cozdas/CozScan2020/Photos/20190418_014314.jpg

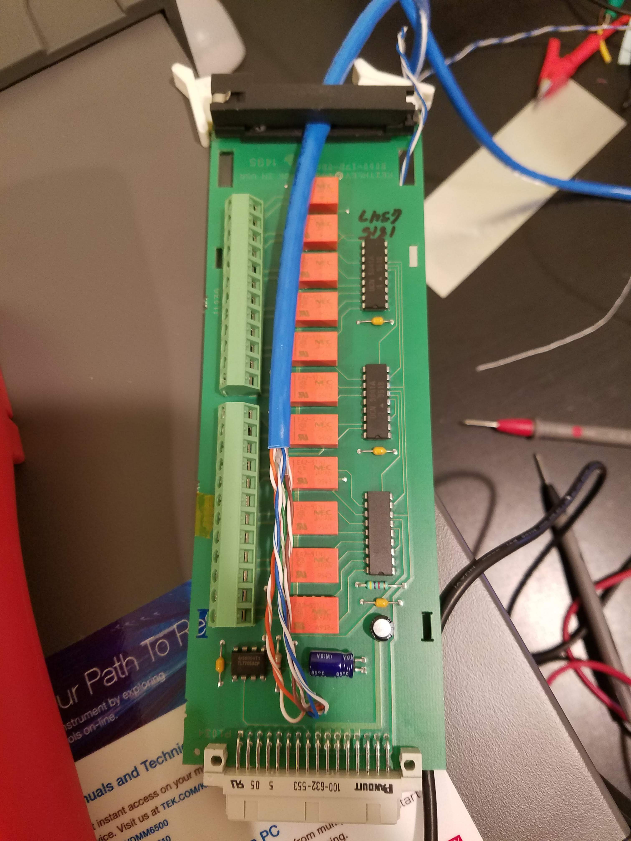
Photos/20190418_014314.jpg
