cozdas/CozScan2020/Photos/20190418_014336.jpg

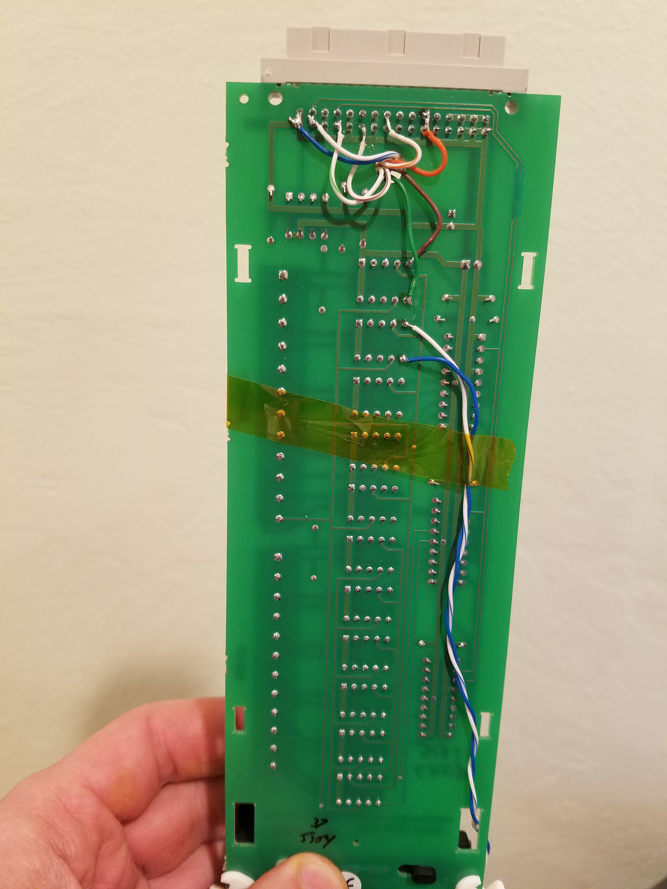
Photos/20190418_014336.jpg
