cozdas/CozScan2020/Photos/20190418_014348.jpg

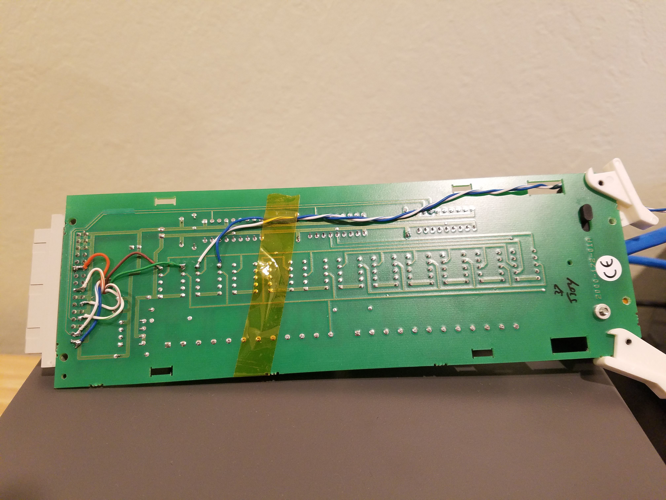
Photos/20190418_014348.jpg
