cozdas/CozScan2020/Photos/20190418_014632.jpg

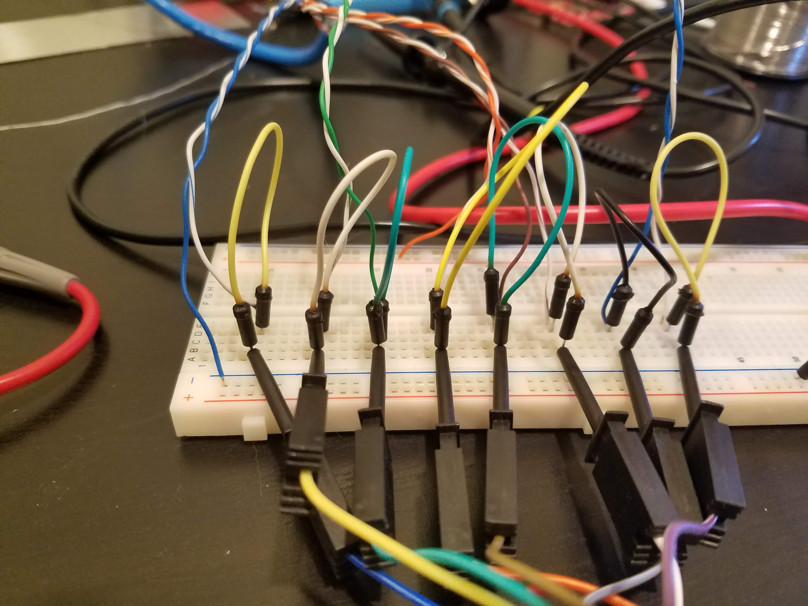
Photos/20190418_014632.jpg
