cozdas/CozScan2020/Photos/20190418_014634.jpg

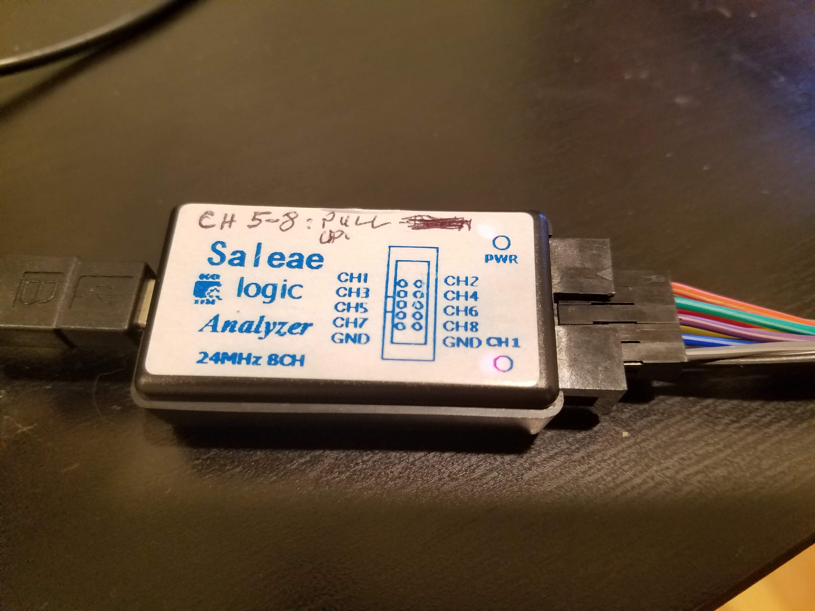
Photos/20190418_014634.jpg
