cozdas/CozScan2020/Photos/20190419_014511.jpg

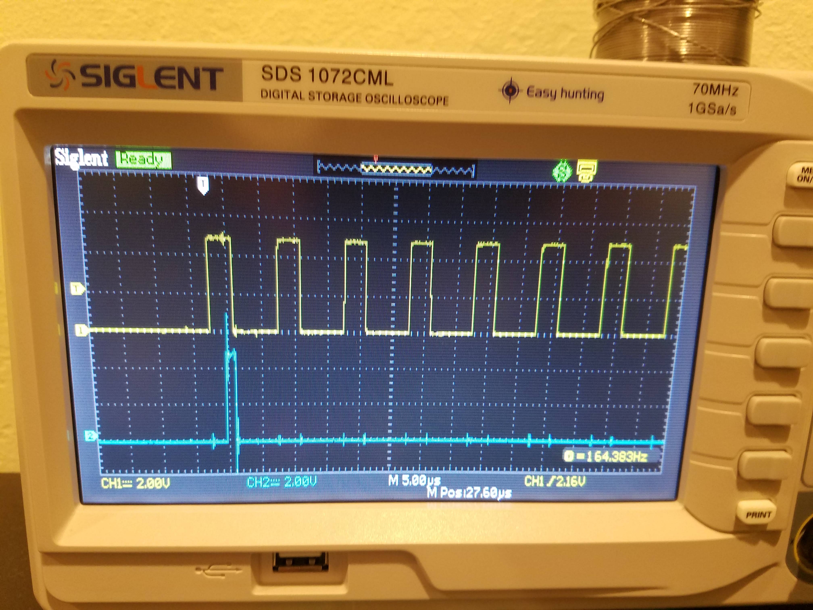
Photos/20190419_014511.jpg
