cozdas/CozScan2020/Photos/20190419_014527.jpg

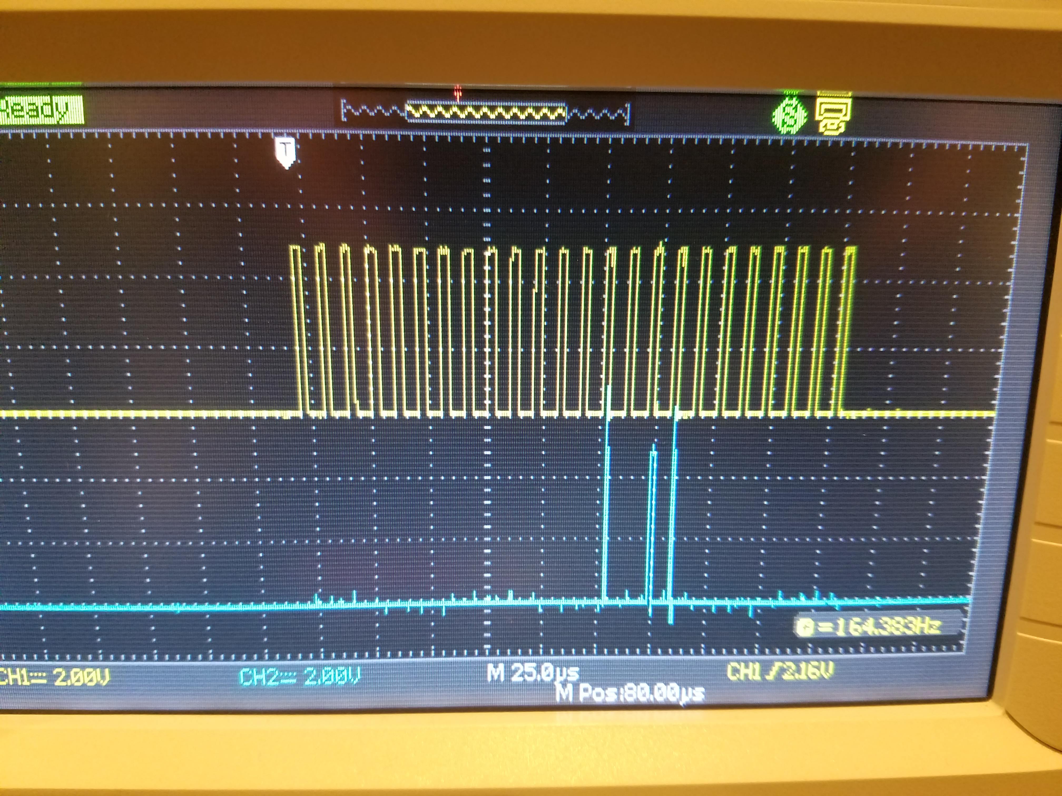
Photos/20190419_014527.jpg
