cozdas/CozScan2020/Photos/20190504_023727.jpg

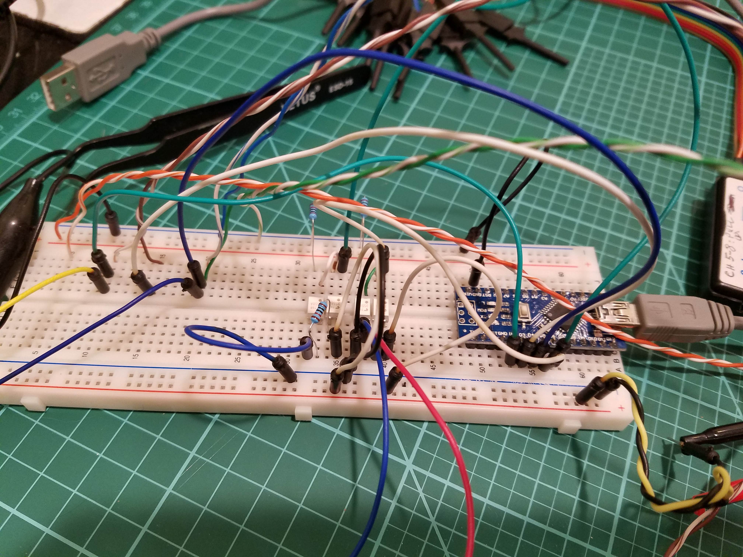
Photos/20190504_023727.jpg
