cozdas/CozScan2020/Photos/20190504_023732.jpg

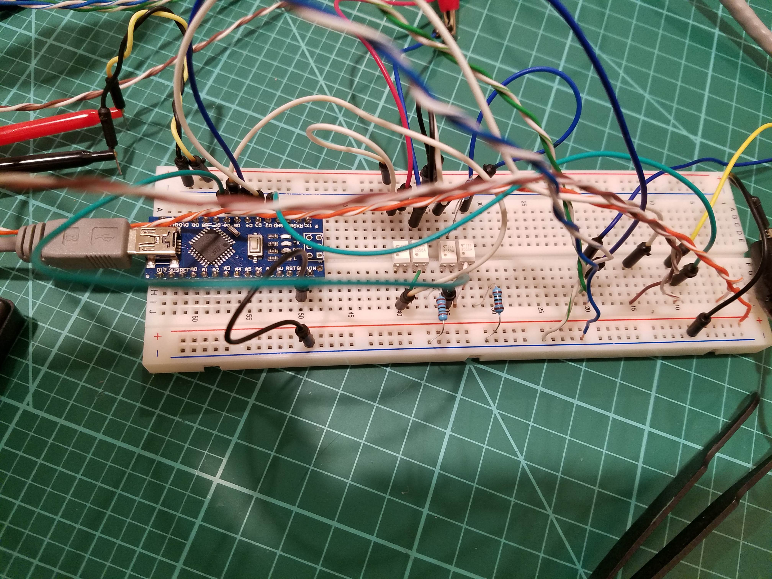
Photos/20190504_023732.jpg
