cozdas/CozScan2020/Photos/20190504_023738.jpg

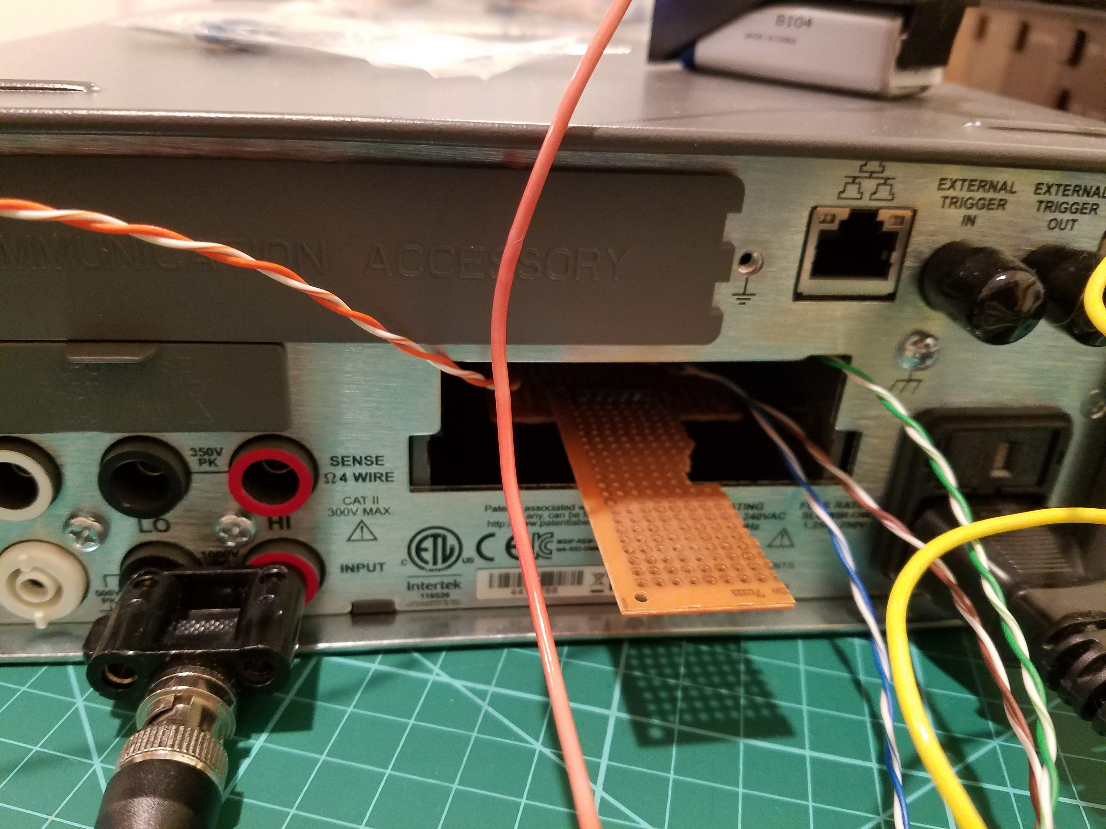
Photos/20190504_023738.jpg
