cozdas/CozScan2020/Photos/20190507_173310.jpg

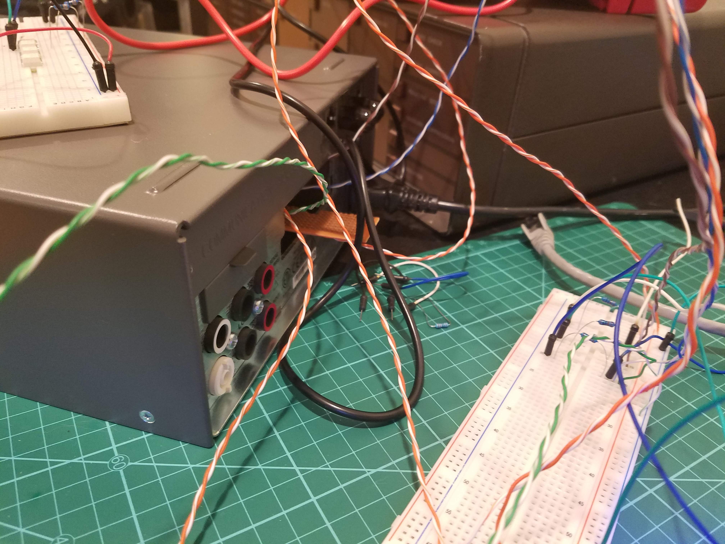
Photos/20190507_173310.jpg
