cozdas/CozScan2020/Photos/20190507_173314.jpg

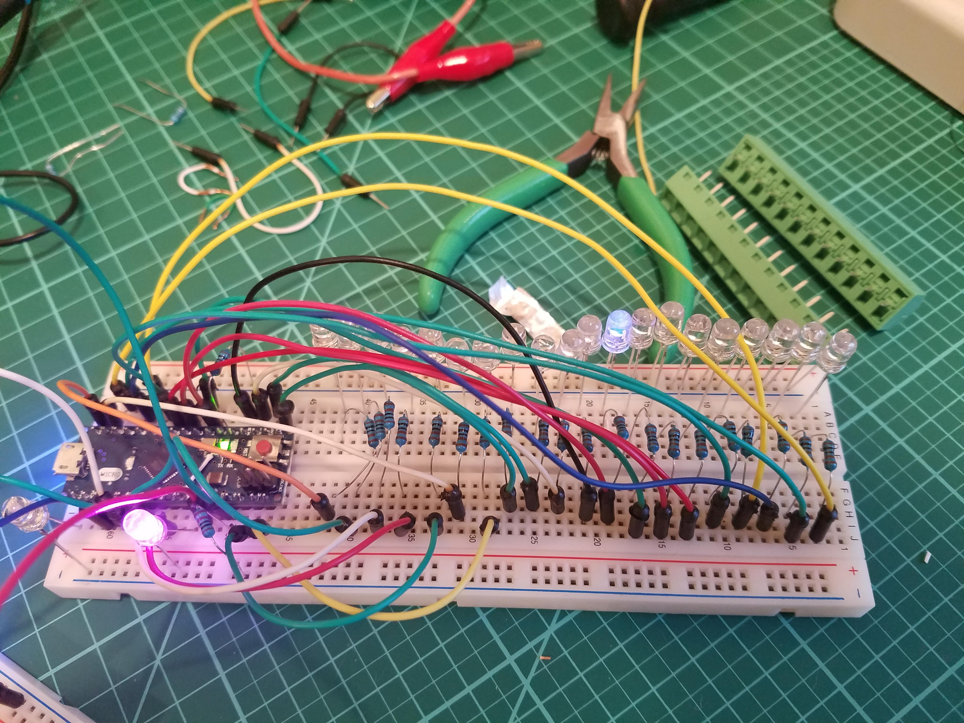
Photos/20190507_173314.jpg
