cozdas/CozScan2020/Photos/20190507_173317.jpg

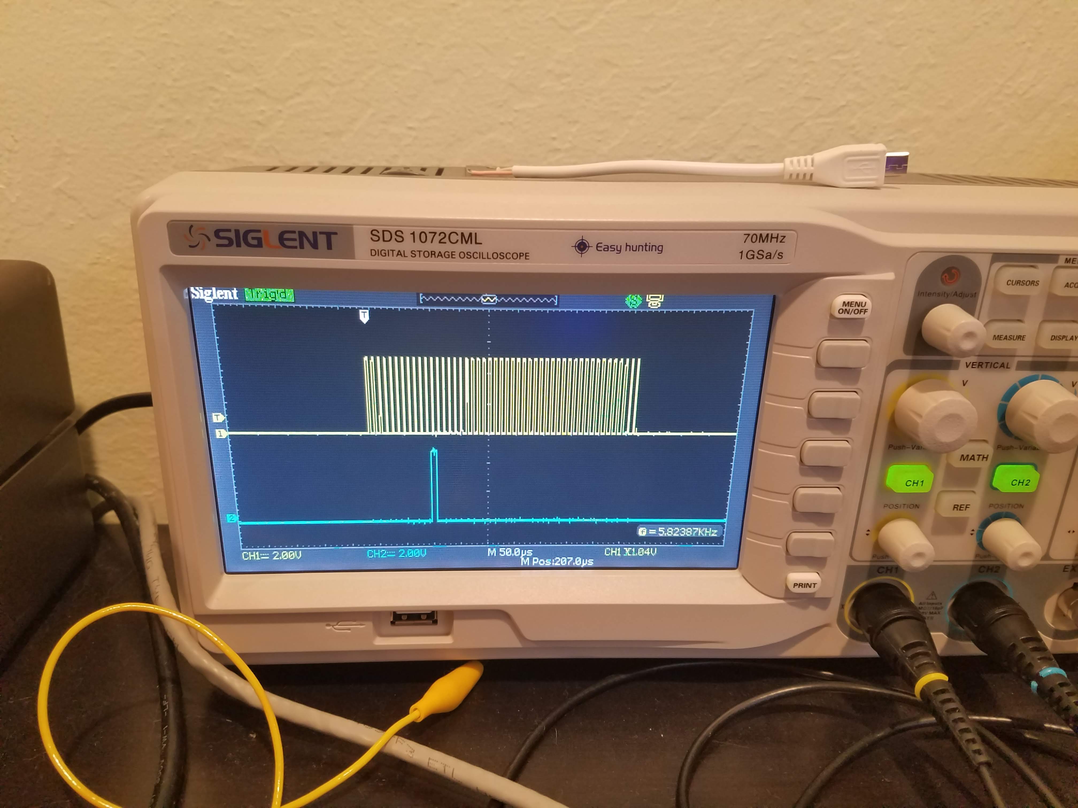
Photos/20190507_173317.jpg
