cozdas/CozScan2020/Photos/20190507_180959.jpg

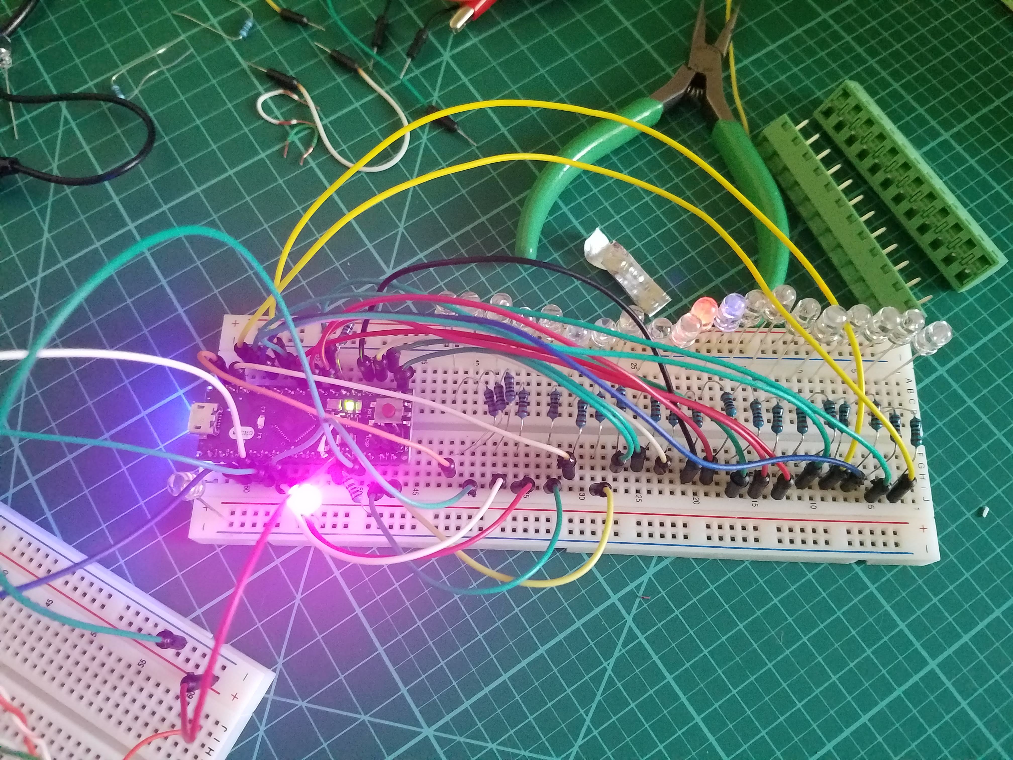
Photos/20190507_180959.jpg
