cozdas/CozScan2020/Photos/20190507_181006.jpg

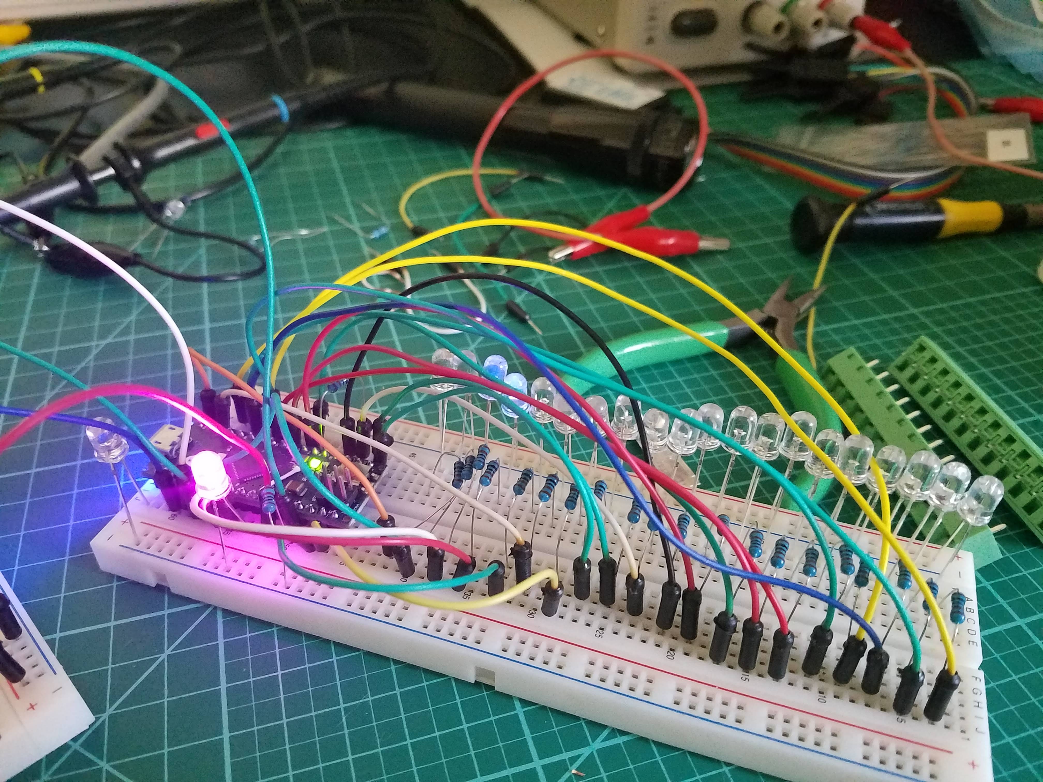
Photos/20190507_181006.jpg
