cozdas/CozScan2020/Photos/20190507_181008.jpg

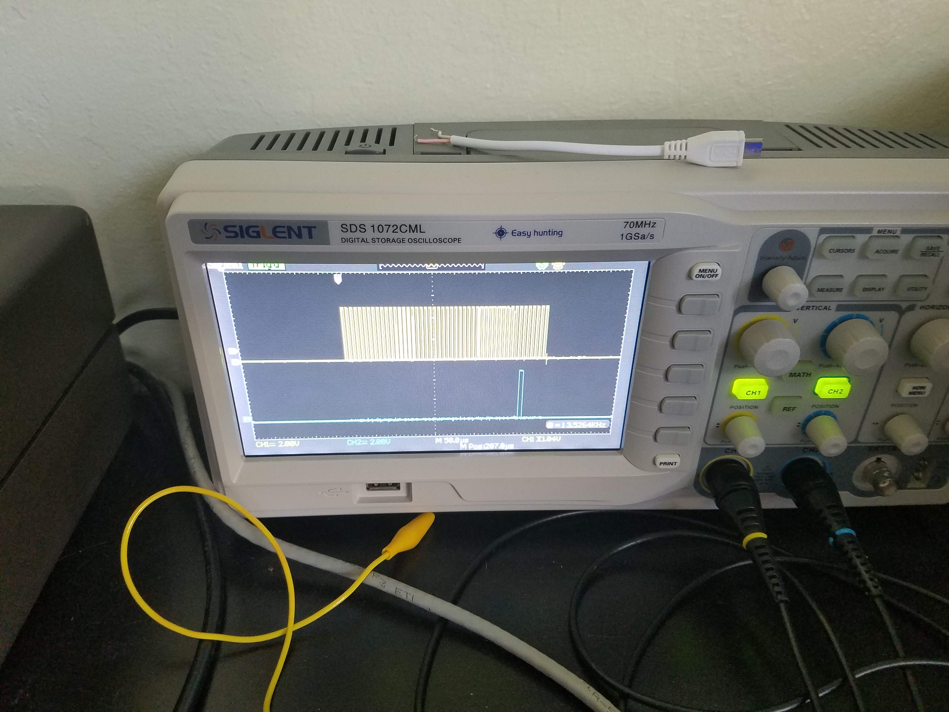
Photos/20190507_181008.jpg
