cozdas/CozScan2020/Photos/20190508_041642.jpg

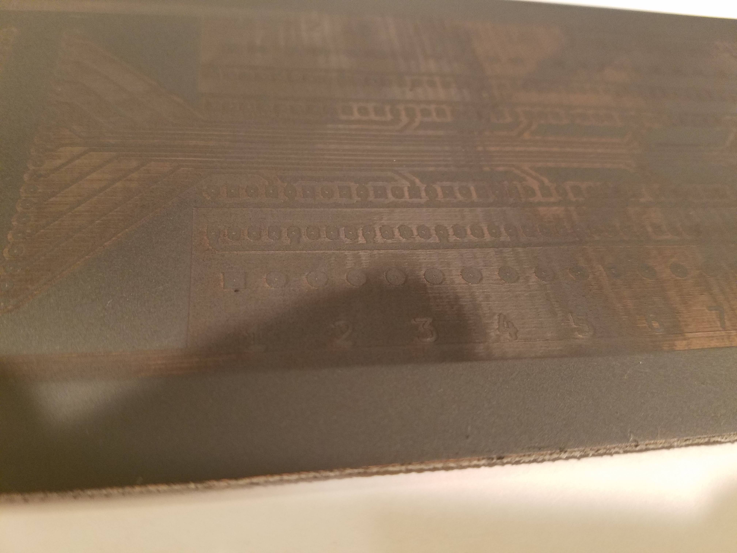
Photos/20190508_041642.jpg
