cozdas/CozScan2020/Photos/20190508_041654.jpg

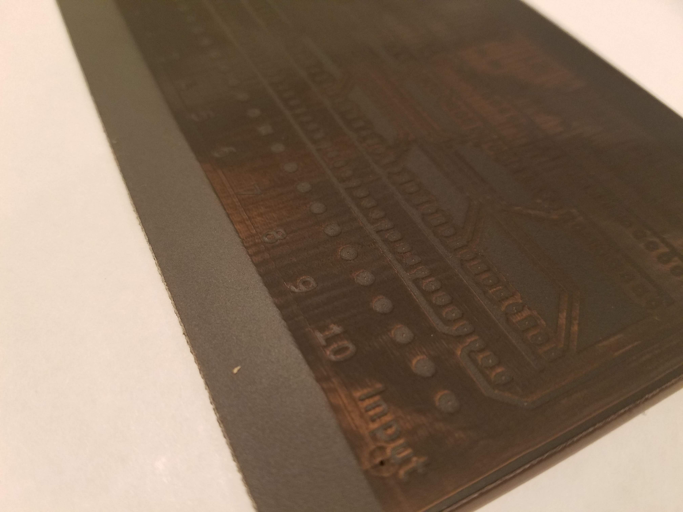
Photos/20190508_041654.jpg
