cozdas/CozScan2020/Photos/20190508_041701.jpg

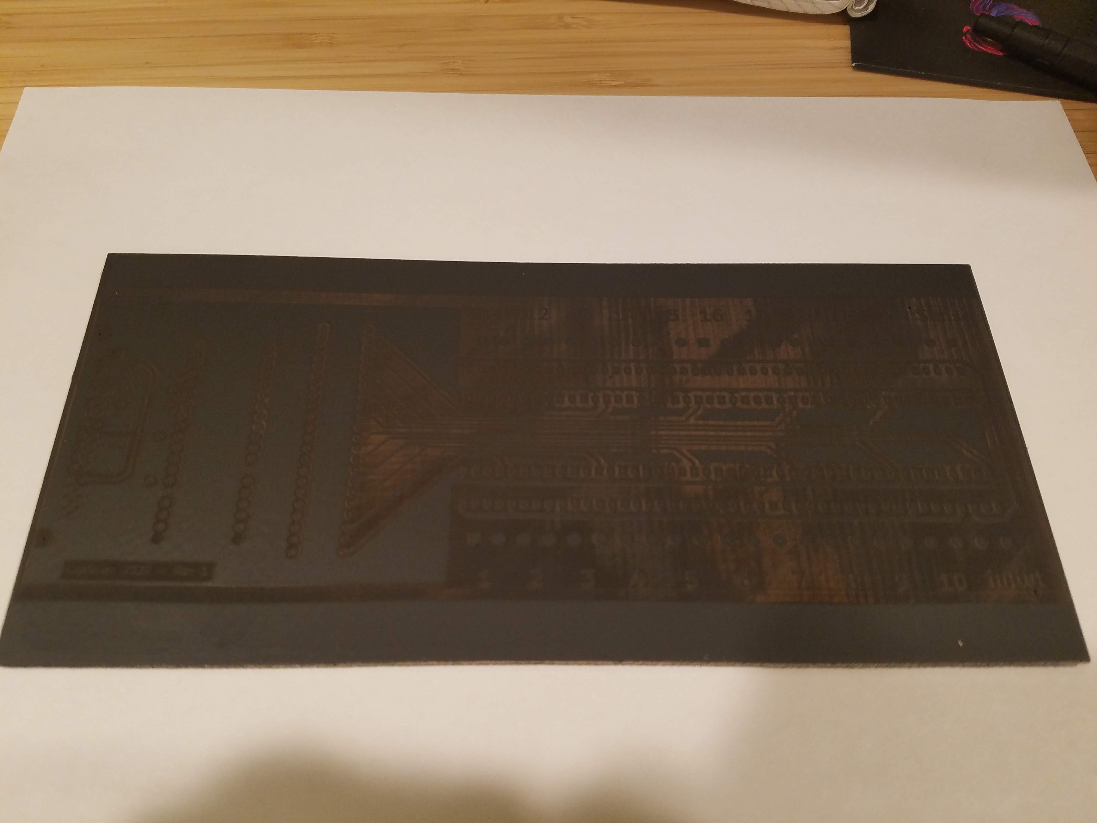
Photos/20190508_041701.jpg
