cozdas/CozScan2020/Photos/20190508_041709.jpg

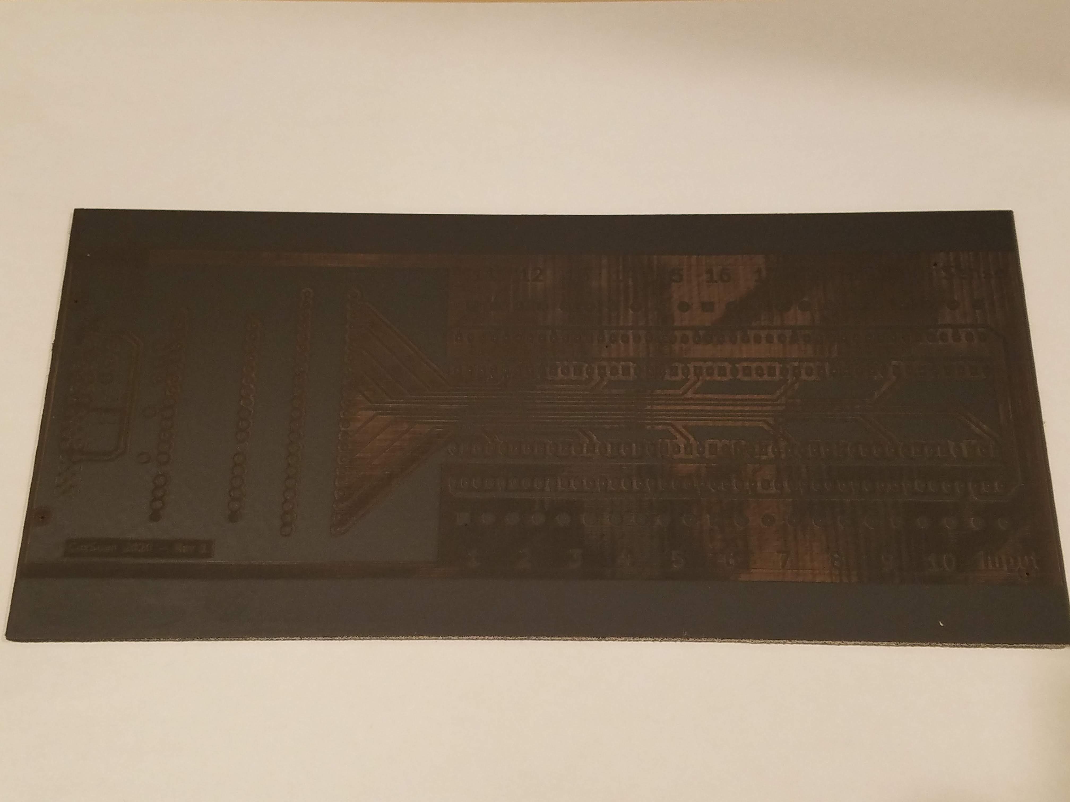
Photos/20190508_041709.jpg
