cozdas/CozScan2020/Photos/20190508_041718.jpg

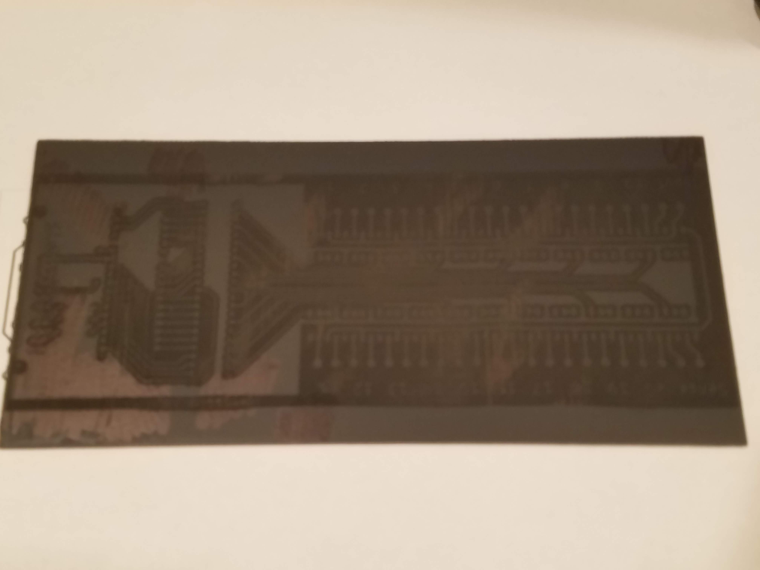
Photos/20190508_041718.jpg
