cozdas/CozScan2020/Photos/20190508_041728.jpg

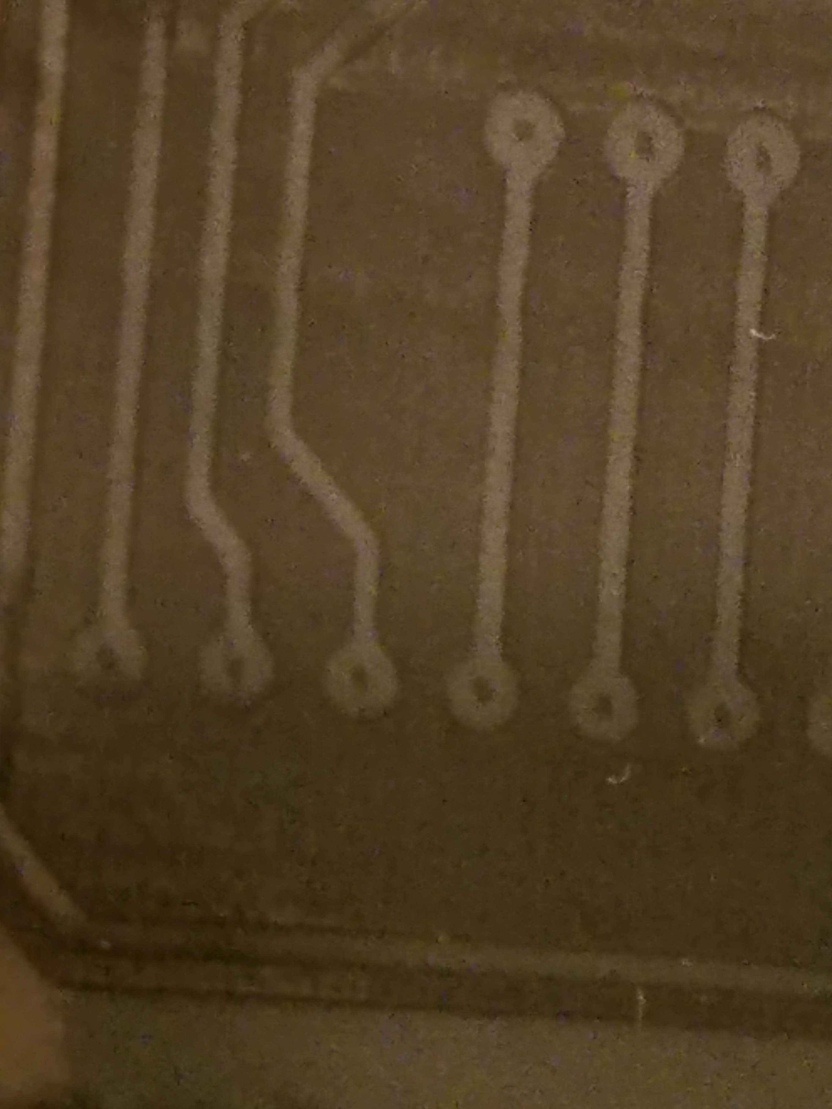
Photos/20190508_041728.jpg
