cozdas/CozScan2020/Photos/20190508_041800.jpg

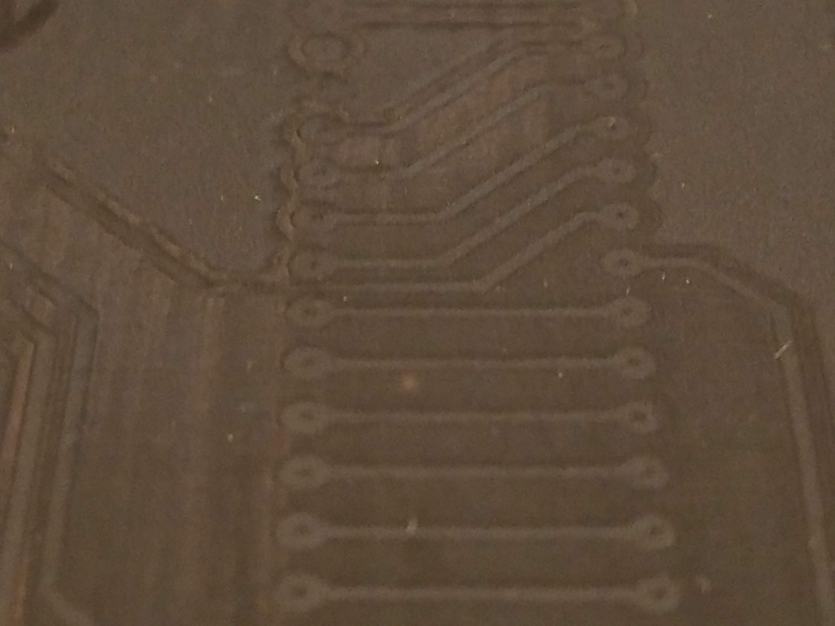
Photos/20190508_041800.jpg
