cozdas/CozScan2020/Photos/20190508_041806.jpg

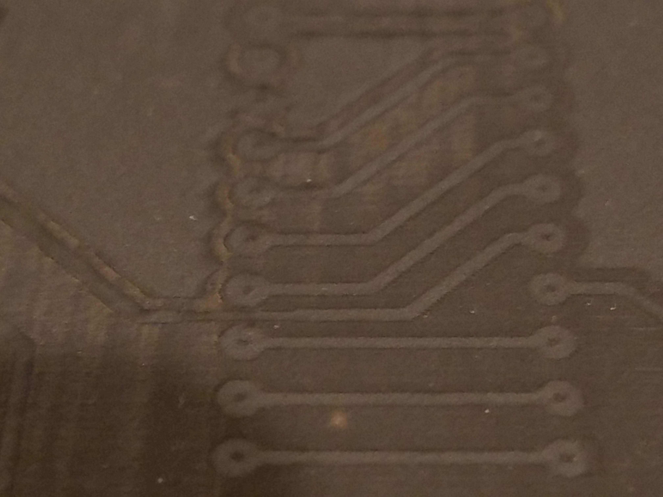
Photos/20190508_041806.jpg
