cozdas/CozScan2020/Photos/20190508_041815.jpg

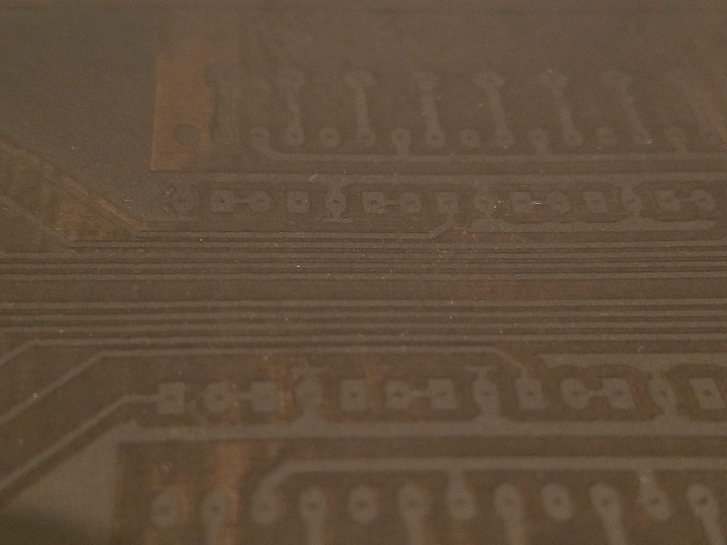
Photos/20190508_041815.jpg
