cozdas/CozScan2020/Photos/20190508_041832.jpg

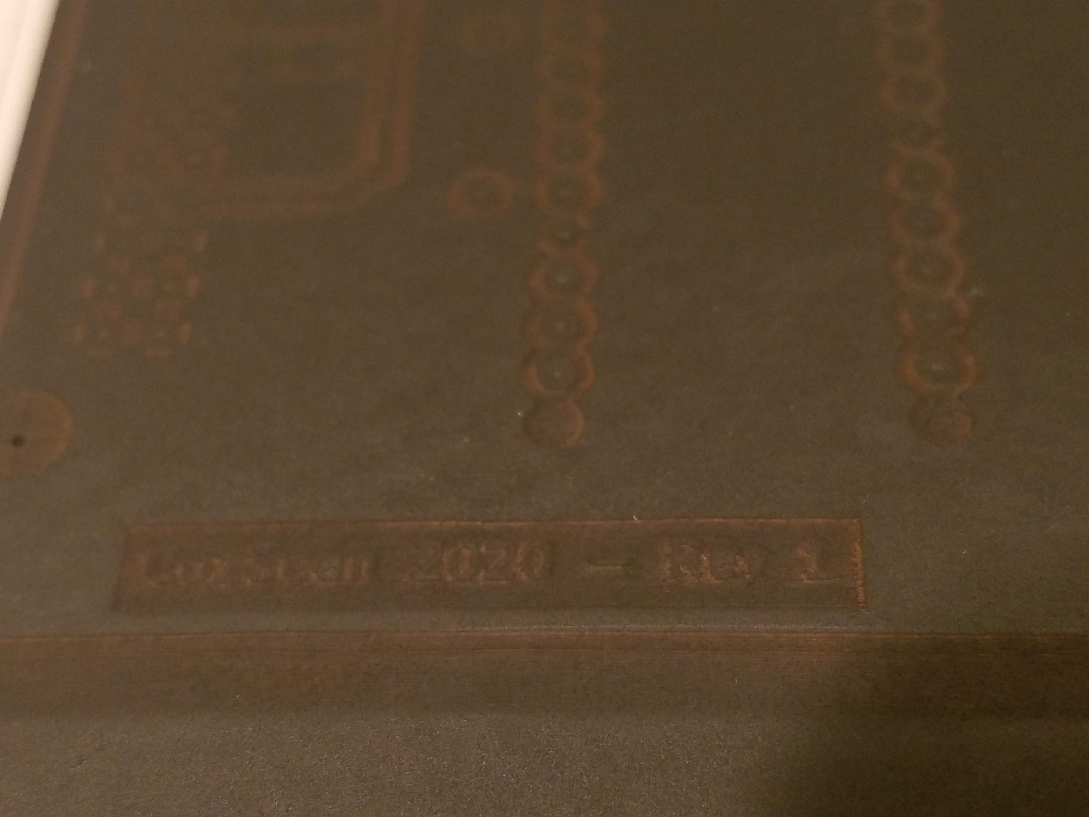
Photos/20190508_041832.jpg
