cozdas/CozScan2020/Photos/20190508_041854.jpg

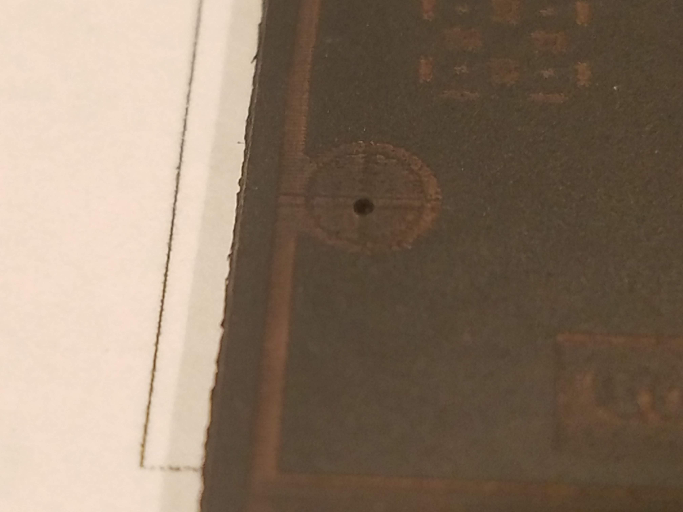
Photos/20190508_041854.jpg
