cozdas/CozScan2020/Photos/20190508_041901.jpg

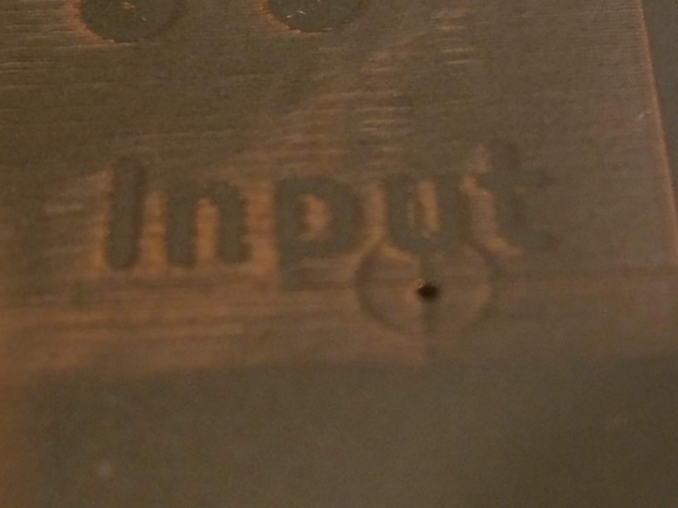
Photos/20190508_041901.jpg
