cozdas/CozScan2020/Photos/20190508_041907.jpg

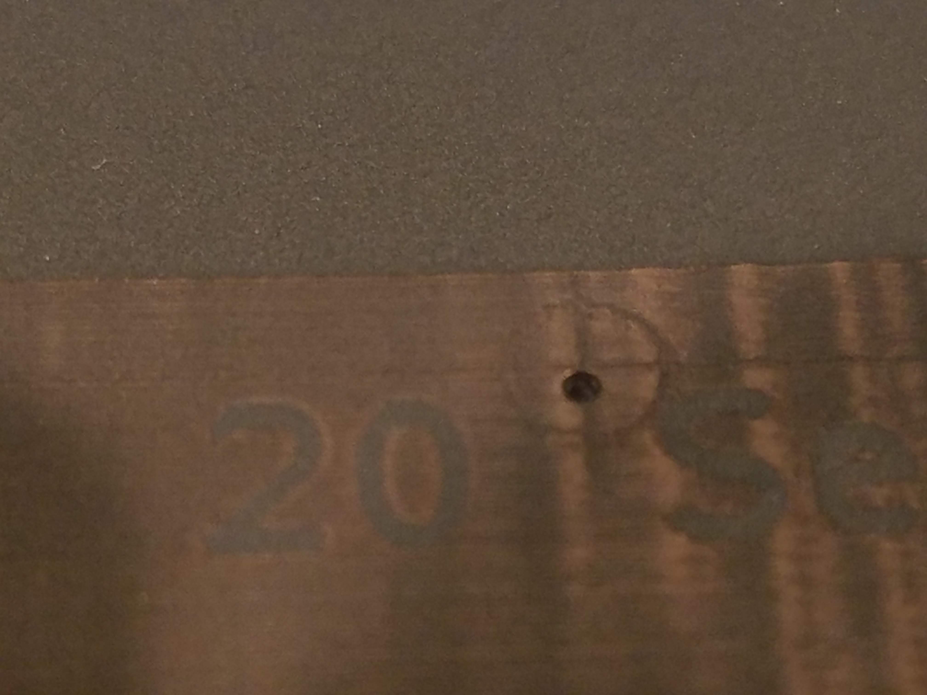
Photos/20190508_041907.jpg
