cozdas/CozScan2020/Photos/20190508_041913.jpg

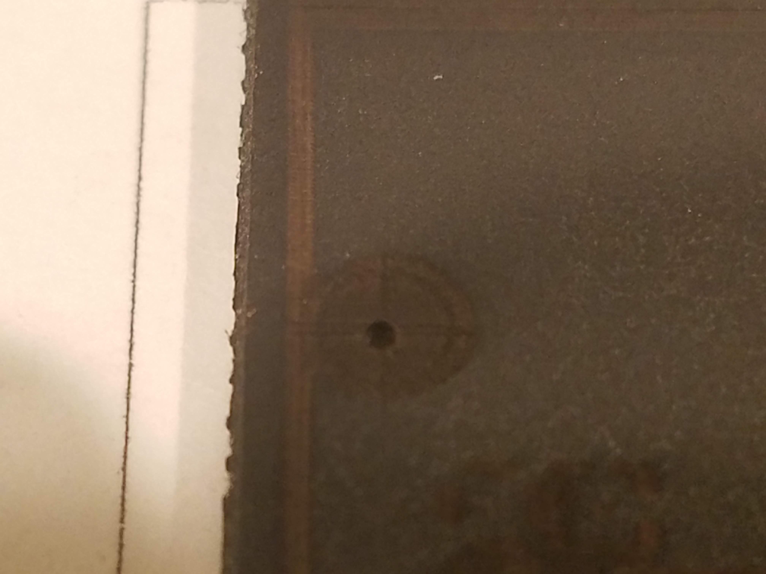
Photos/20190508_041913.jpg
