cozdas/CozScan2020/Photos/20190508_122457.jpg

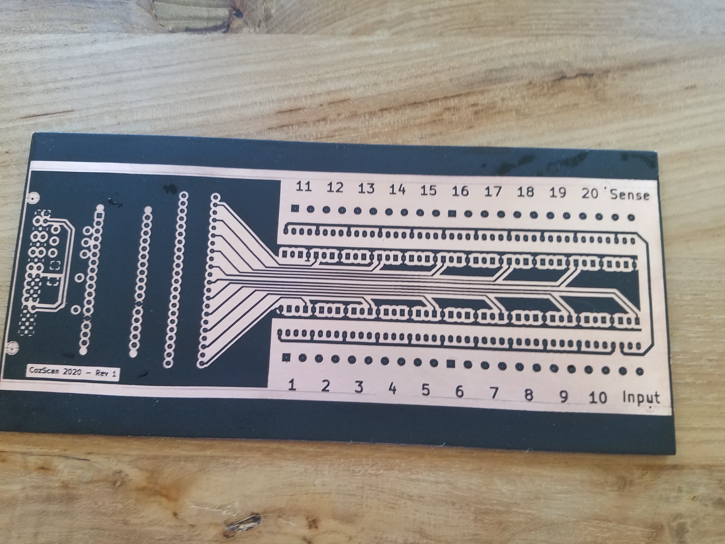
Photos/20190508_122457.jpg
