cozdas/CozScan2020/Photos/20190508_122500.jpg

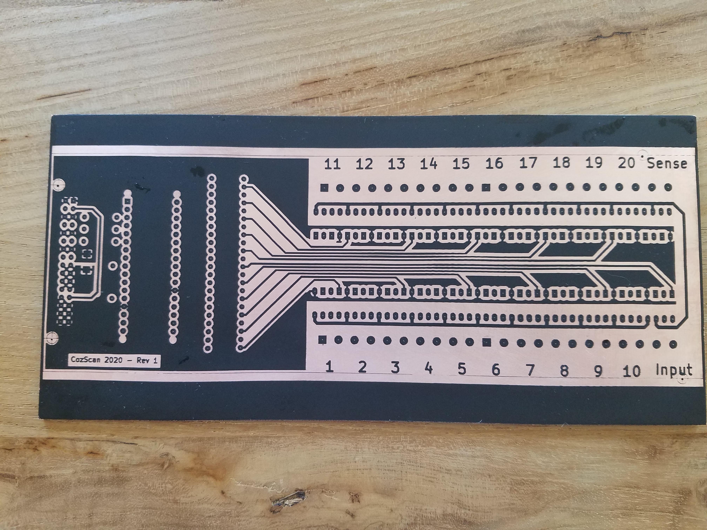
Photos/20190508_122500.jpg
