cozdas/CozScan2020/Photos/20190508_122502.jpg

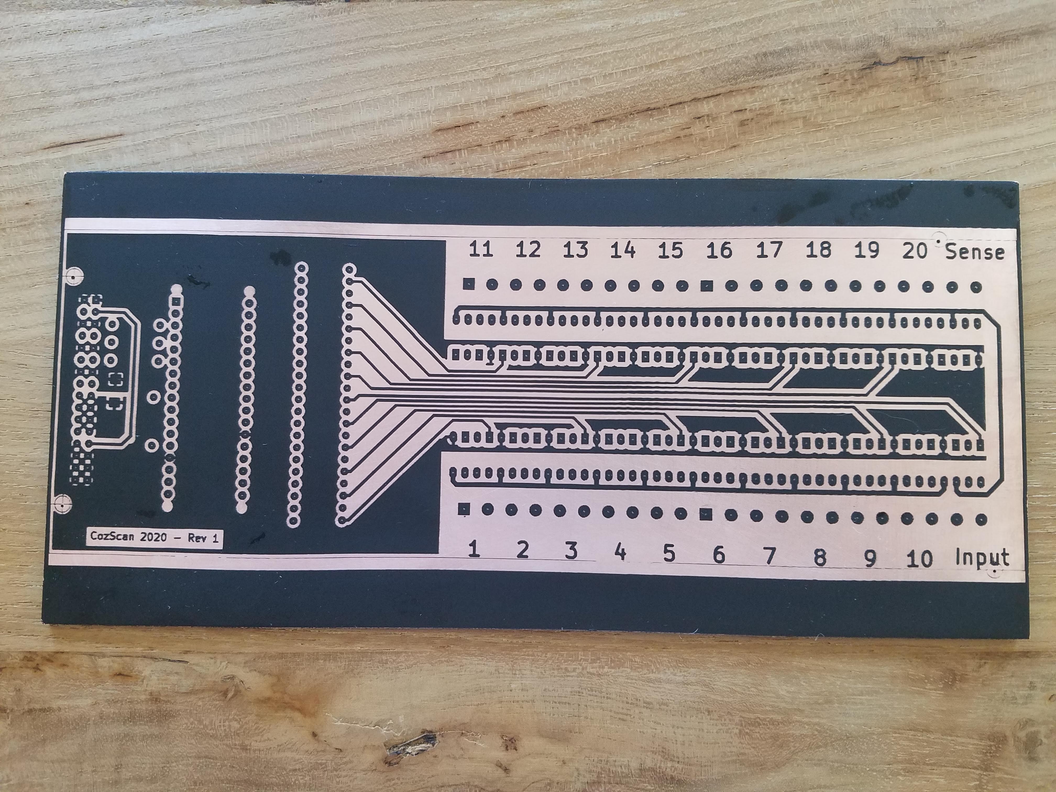
Photos/20190508_122502.jpg
