cozdas/CozScan2020/Photos/20190508_122524.jpg

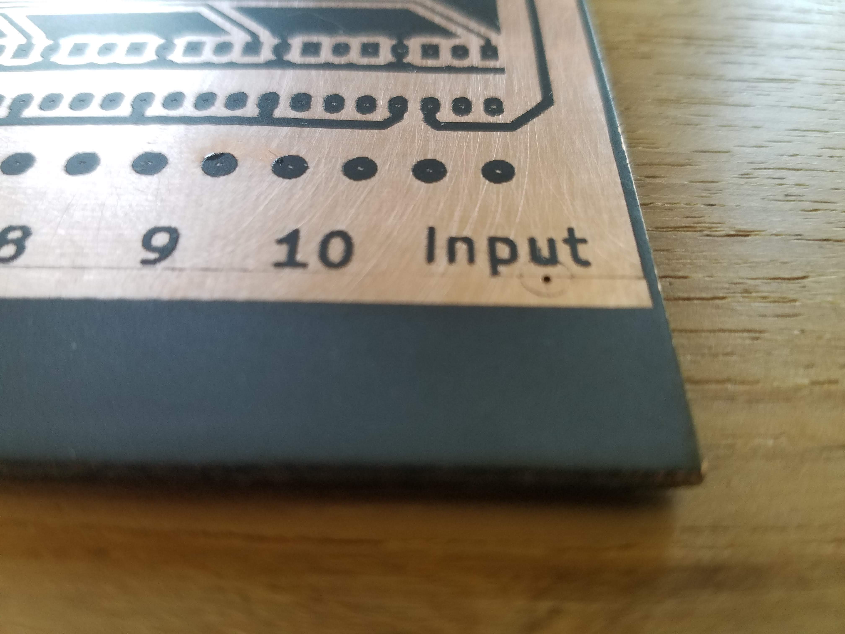
Photos/20190508_122524.jpg
