cozdas/CozScan2020/Photos/20190508_122540.jpg

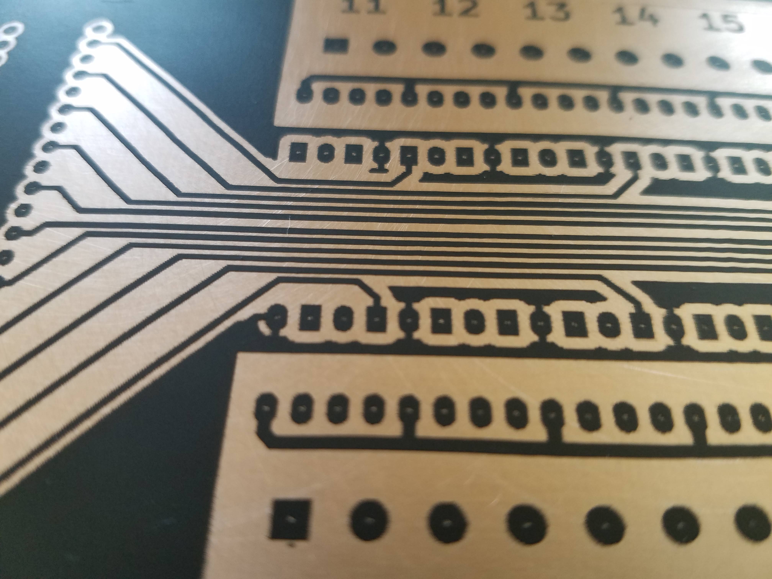
Photos/20190508_122540.jpg
