cozdas/CozScan2020/Photos/20190508_122555.jpg

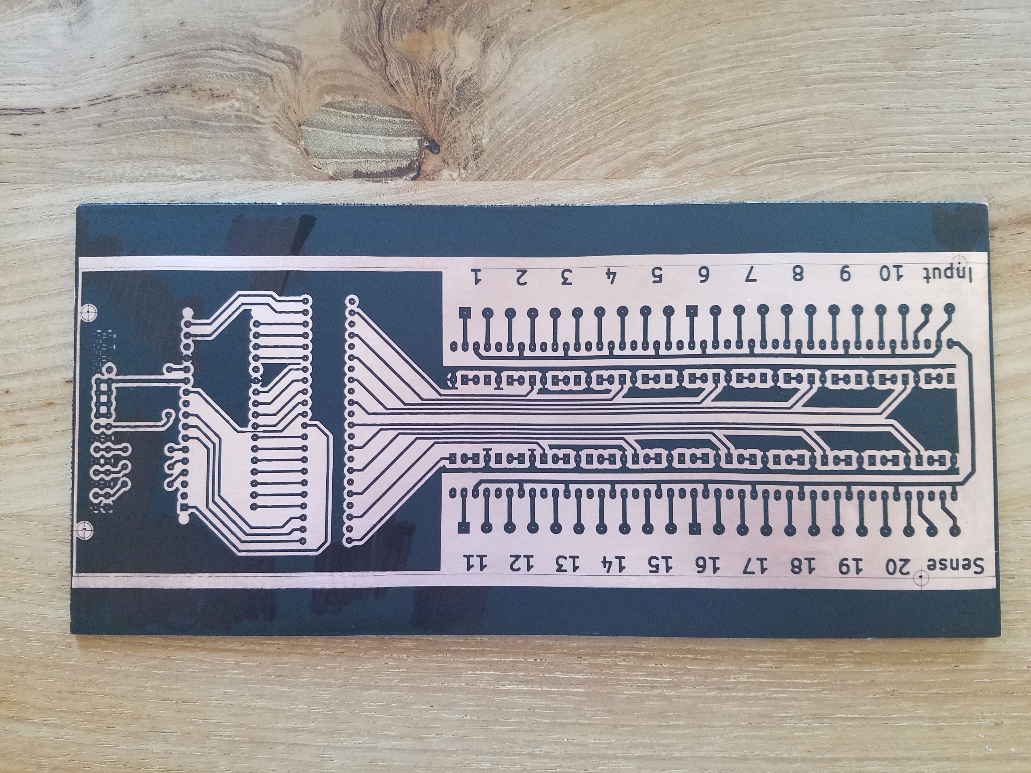
Photos/20190508_122555.jpg
