cozdas/CozScan2020/Photos/20190508_122559.jpg

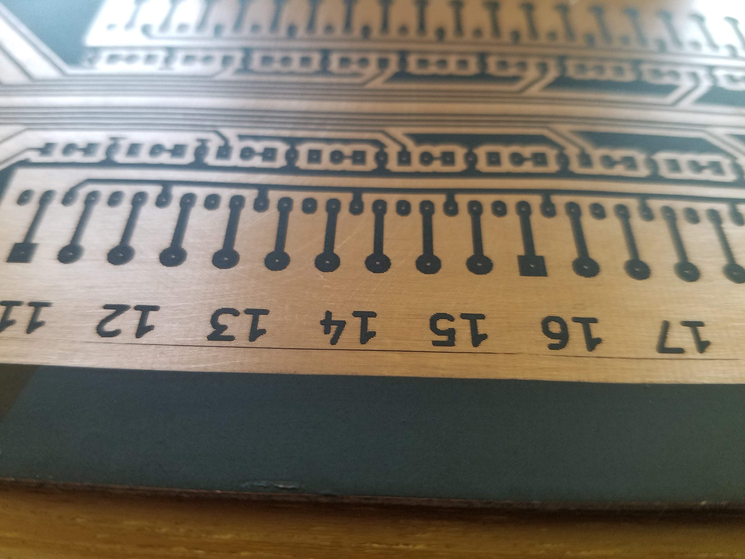
Photos/20190508_122559.jpg
