cozdas/CozScan2020/Photos/20190508_122606.jpg

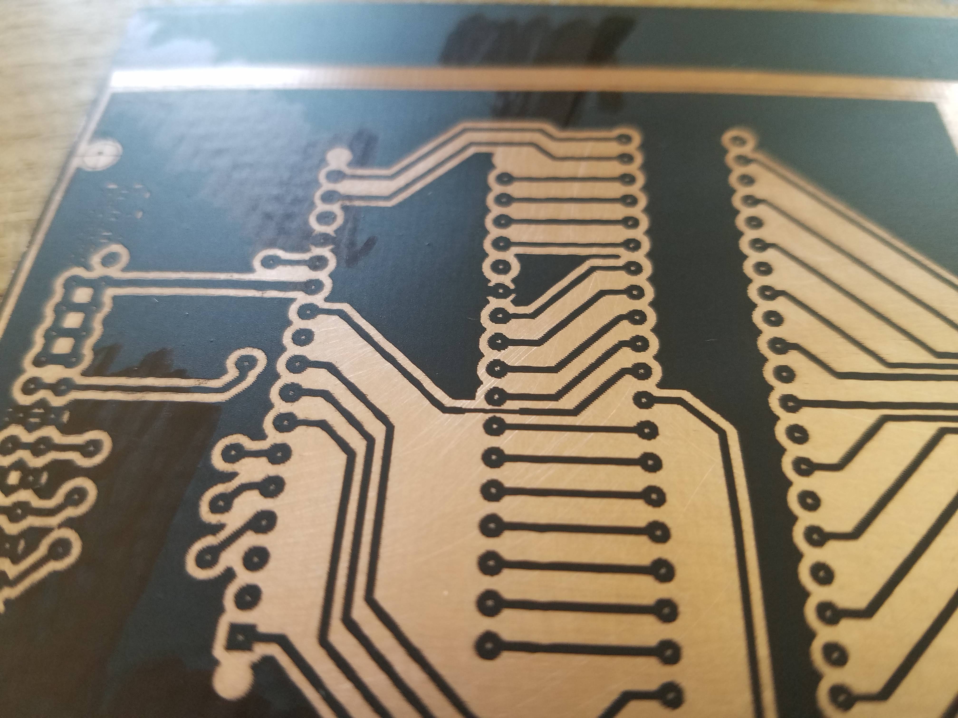
Photos/20190508_122606.jpg
