cozdas/CozScan2020/Photos/20190508_122619.jpg

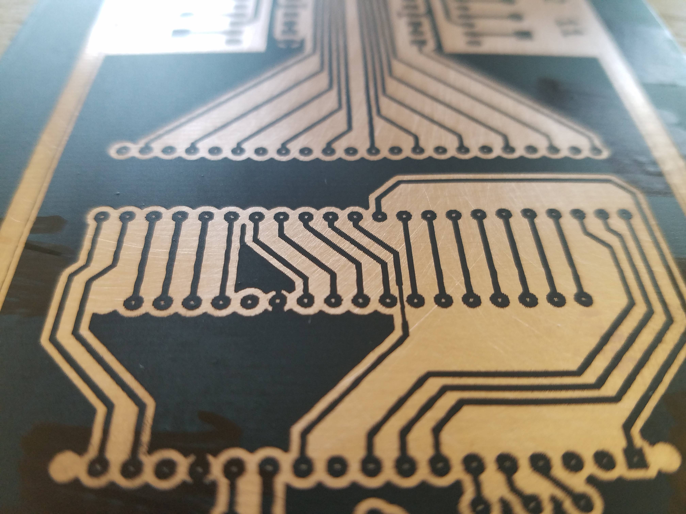
Photos/20190508_122619.jpg
