cozdas/CozScan2020/Photos/20190508_122633.jpg

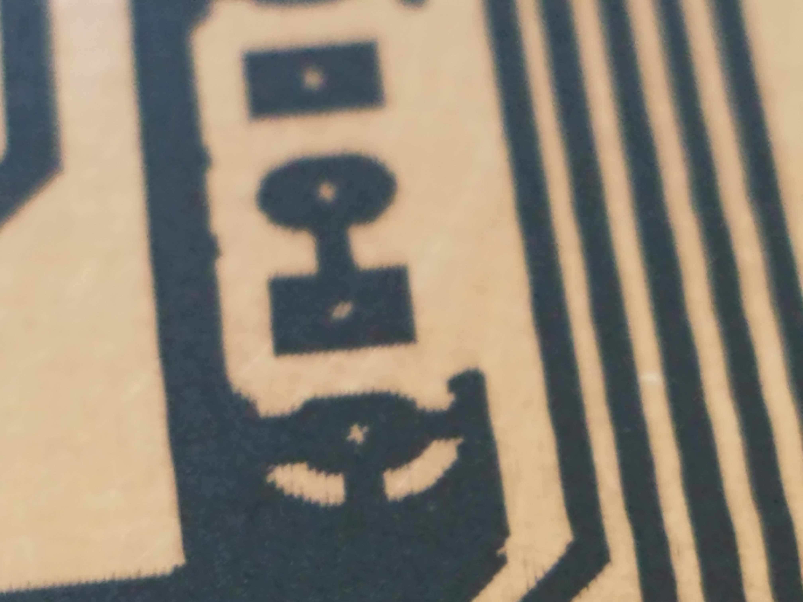
Photos/20190508_122633.jpg
