cozdas/CozScan2020/Photos/20190508_122658.jpg

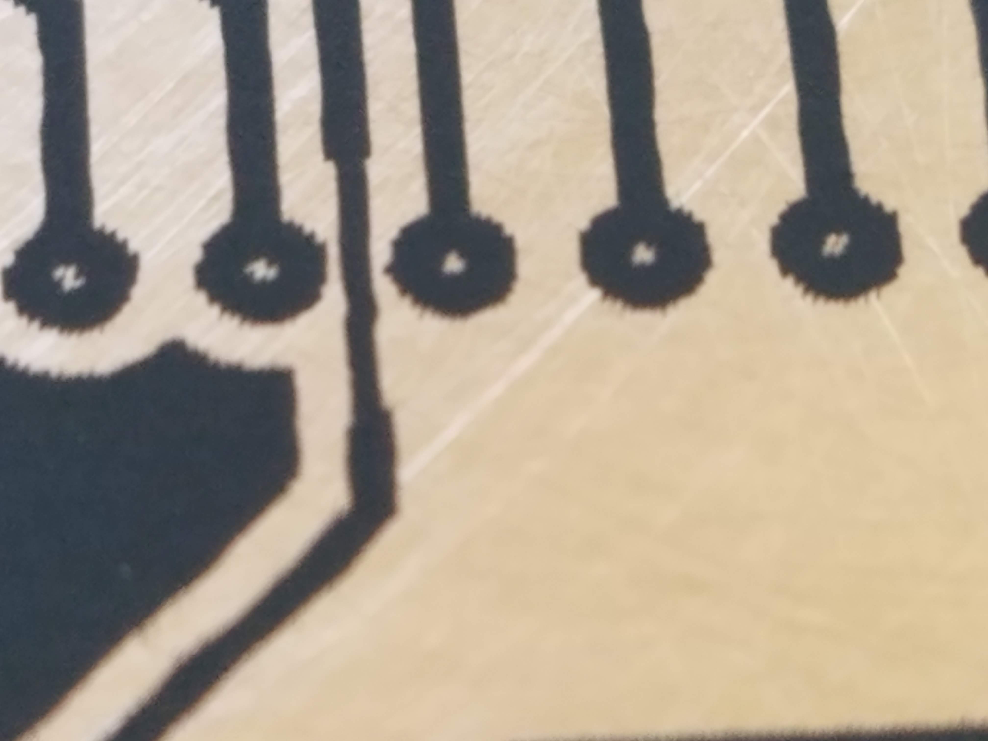
Photos/20190508_122658.jpg
