cozdas/CozScan2020/Photos/20190508_122708.jpg

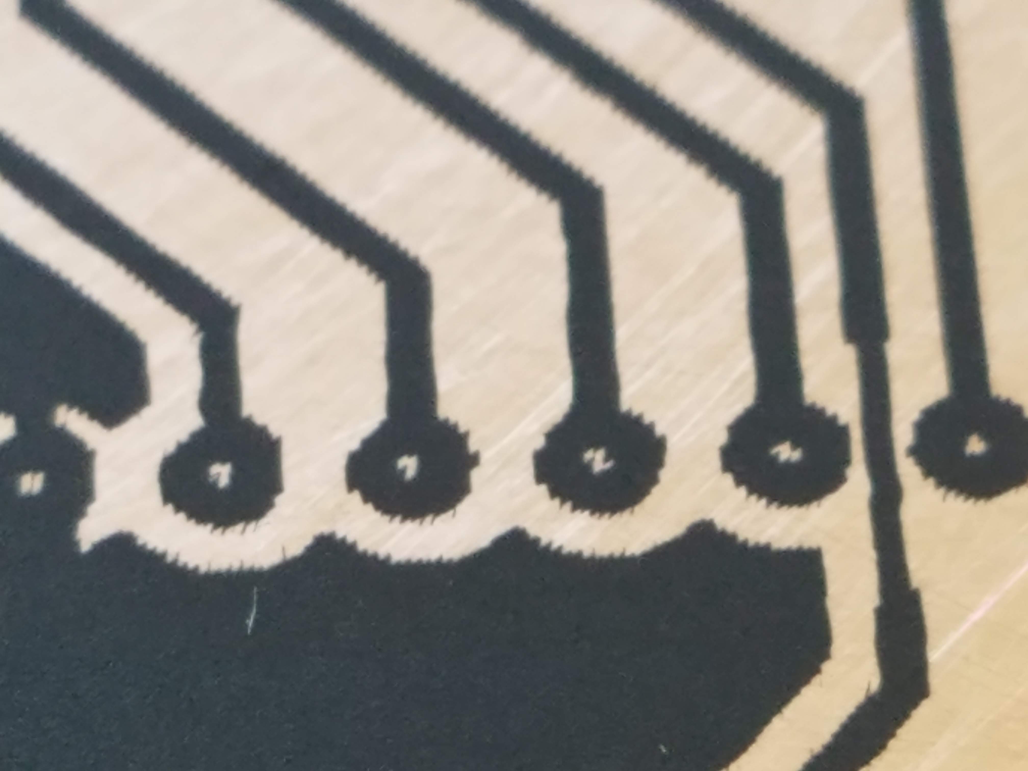
Photos/20190508_122708.jpg
