cozdas/CozScan2020/Photos/20190508_122728.jpg

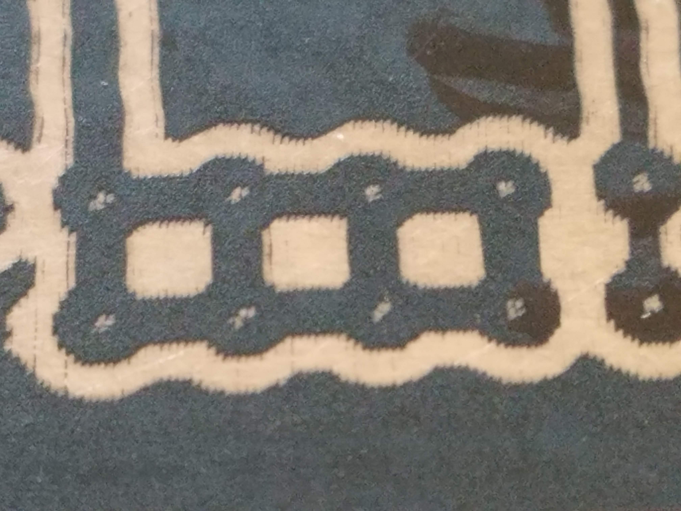
Photos/20190508_122728.jpg
