cozdas/CozScan2020/Photos/20190508_141439.jpg

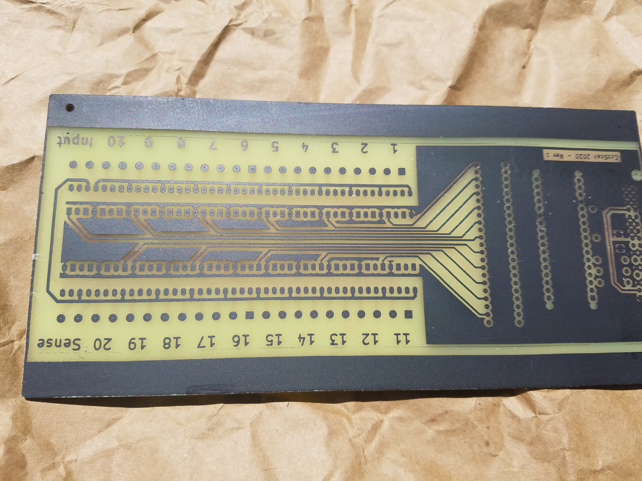
Photos/20190508_141439.jpg
