cozdas/CozScan2020/Photos/20190508_141443.jpg

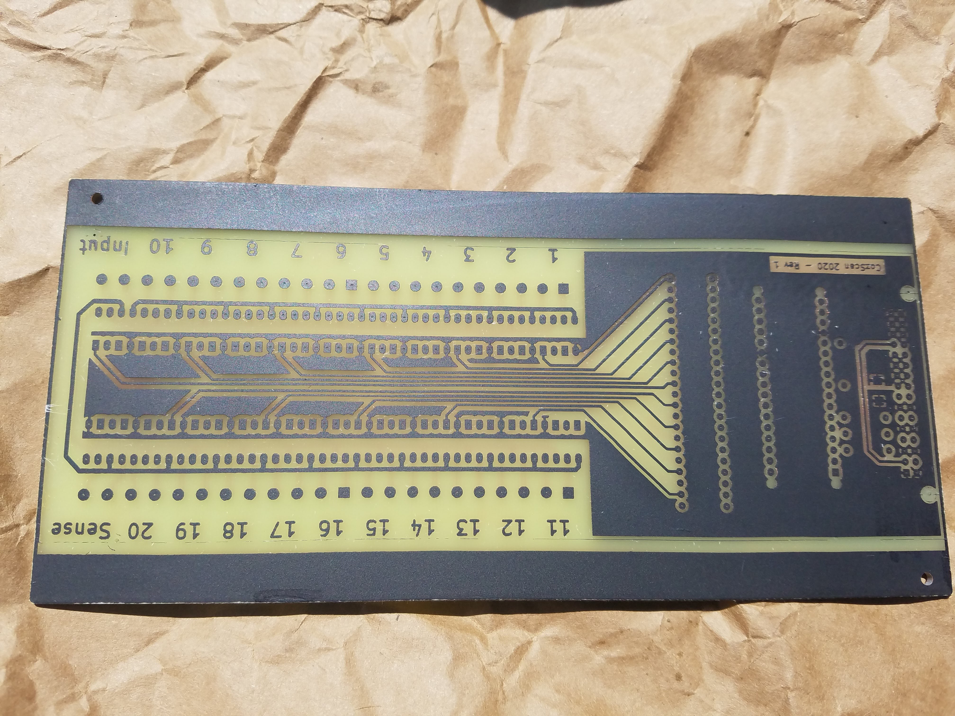
Photos/20190508_141443.jpg
