cozdas/CozScan2020/Photos/20190508_141448.jpg

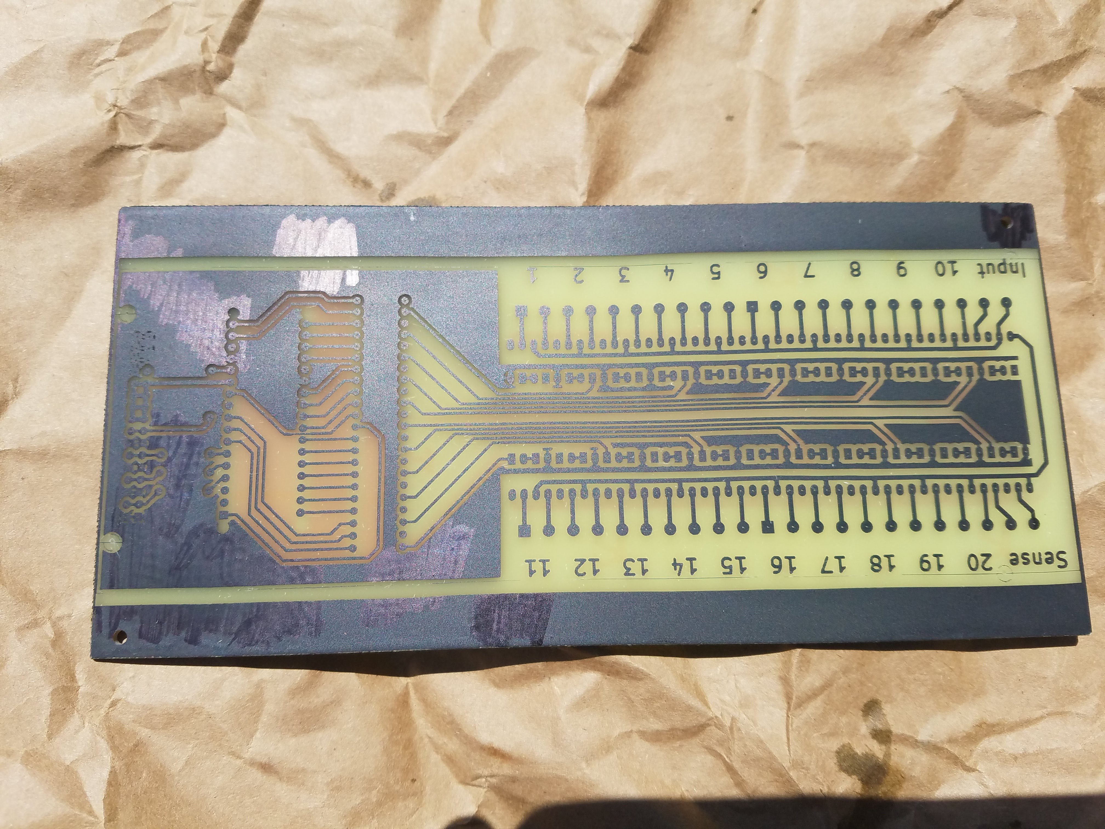
Photos/20190508_141448.jpg
