cozdas/CozScan2020/Photos/20190508_141454.jpg

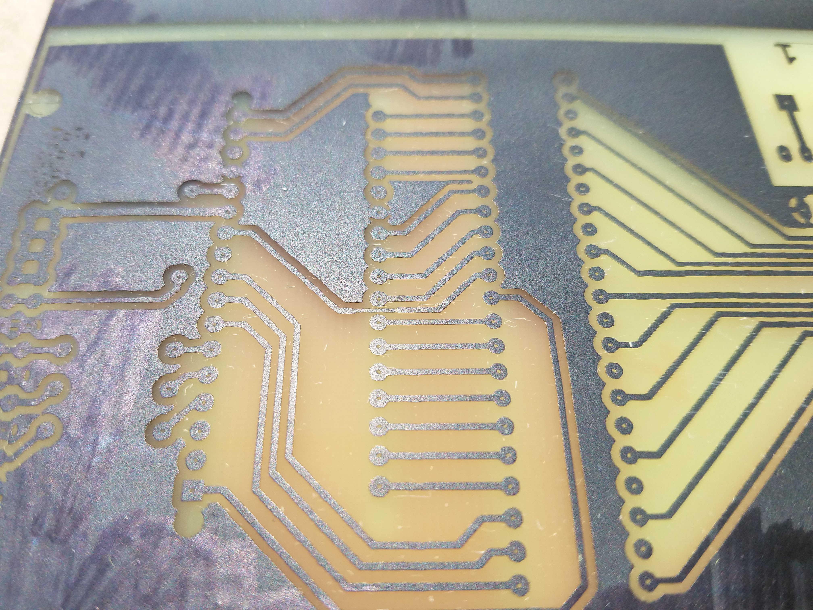
Photos/20190508_141454.jpg
