cozdas/CozScan2020/Photos/20190508_141459.jpg

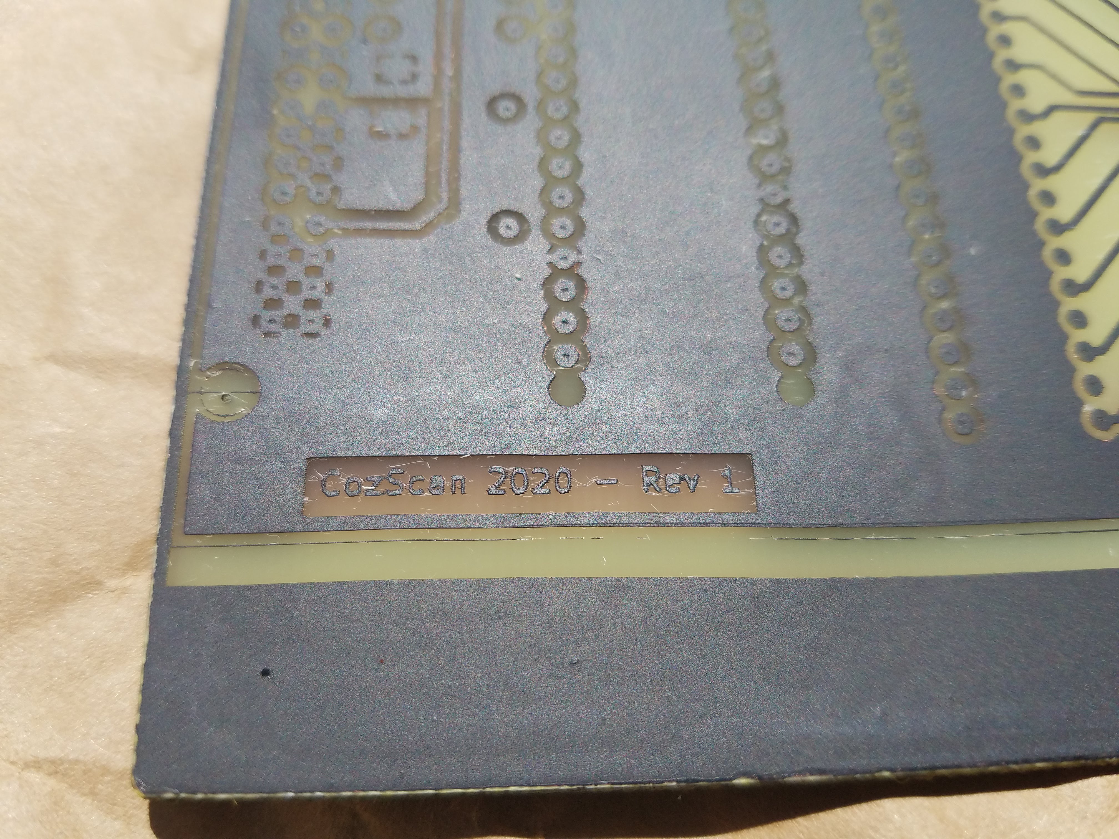
Photos/20190508_141459.jpg
