cozdas/CozScan2020/Photos/20190508_142113.jpg

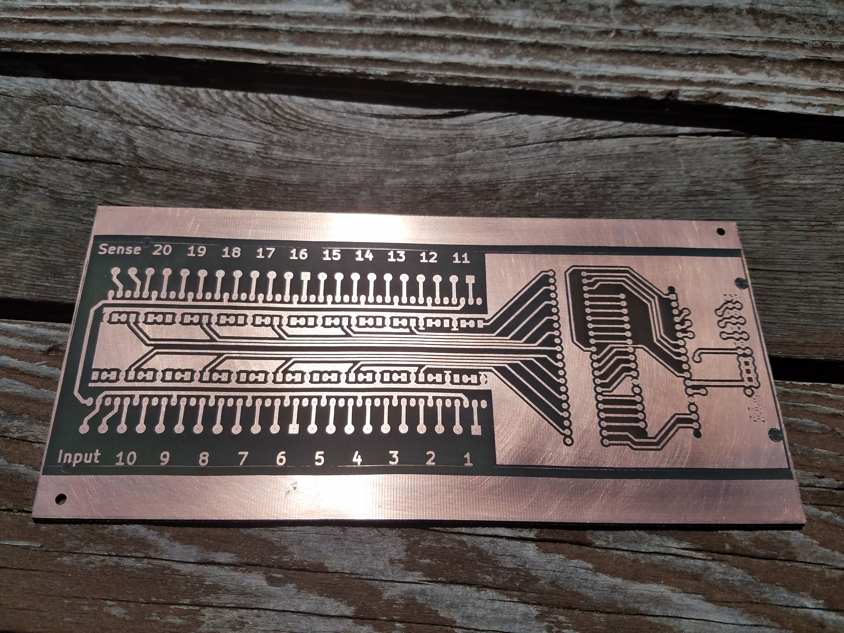
Photos/20190508_142113.jpg
