cozdas/CozScan2020/Photos/20190508_142119.jpg

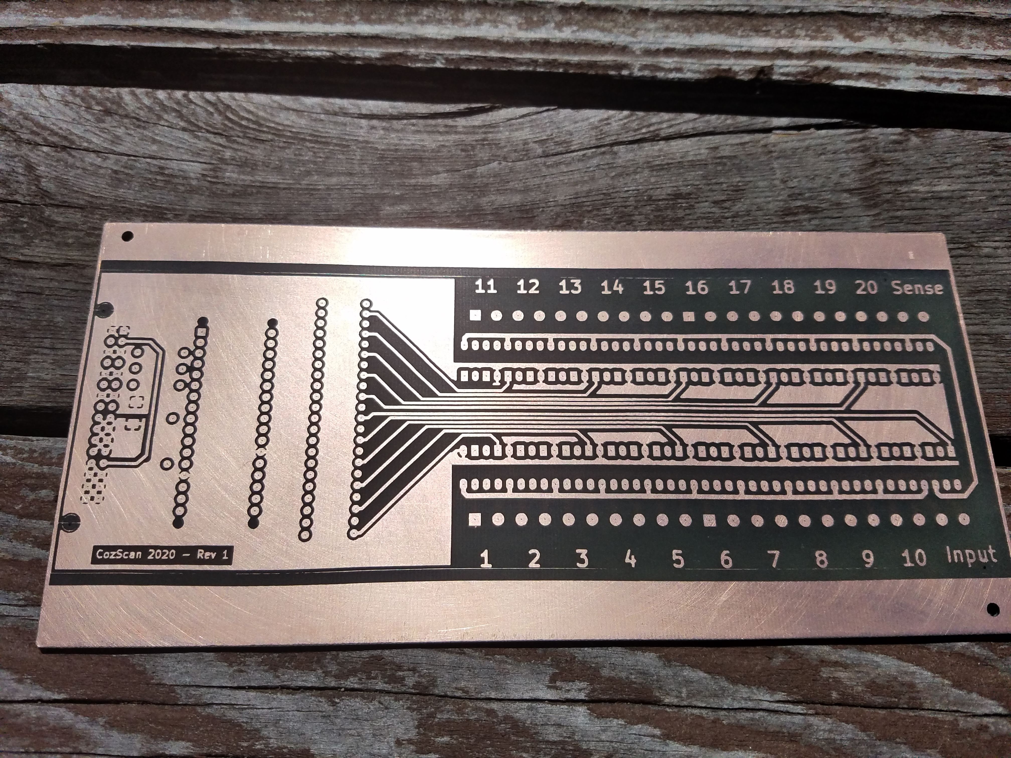
Photos/20190508_142119.jpg
