cozdas/CozScan2020/Photos/20190508_142126.jpg

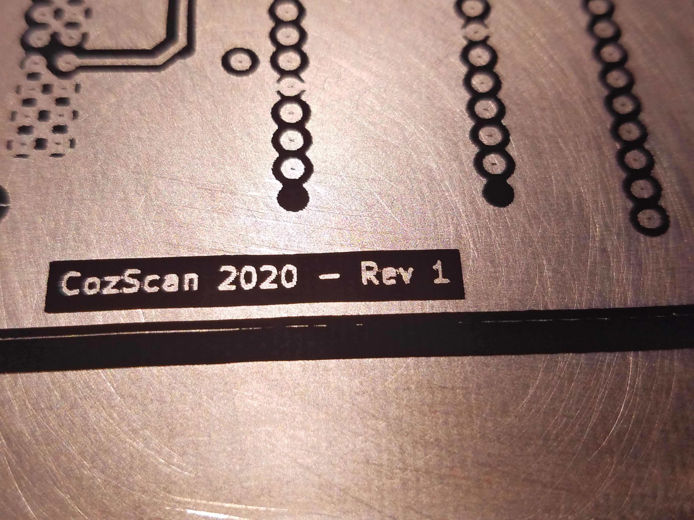
Photos/20190508_142126.jpg
