cozdas/CozScan2020/Photos/20190508_142127.jpg

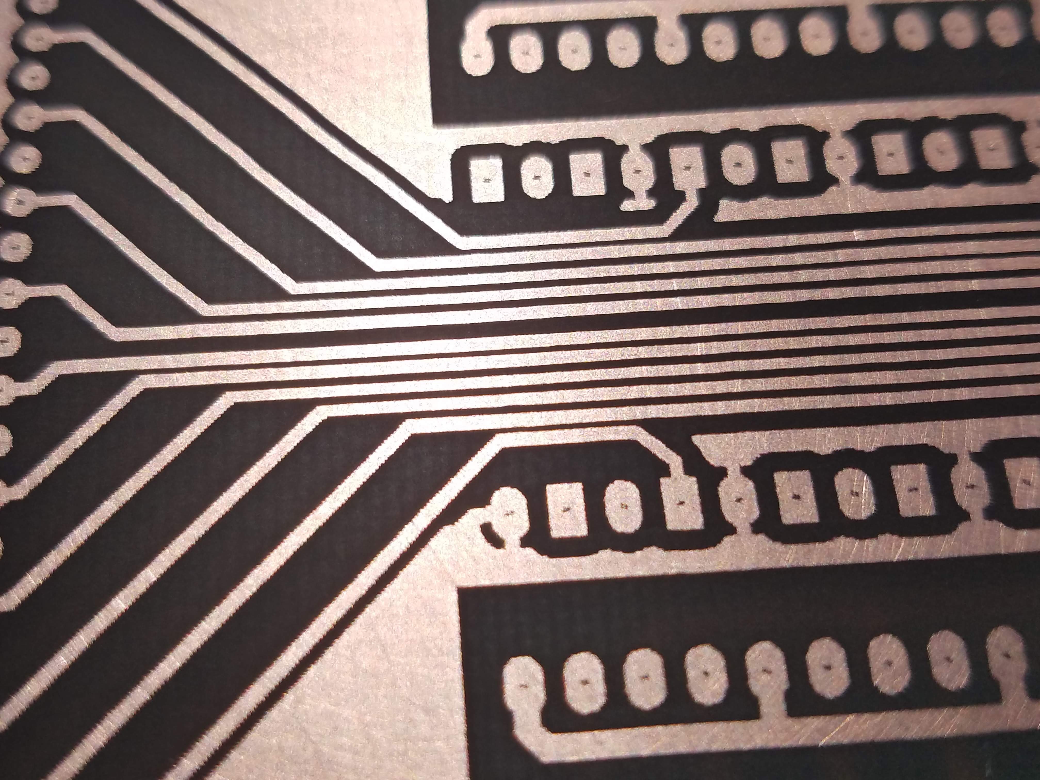
Photos/20190508_142127.jpg
