cozdas/CozScan2020/Photos/20190508_142134.jpg

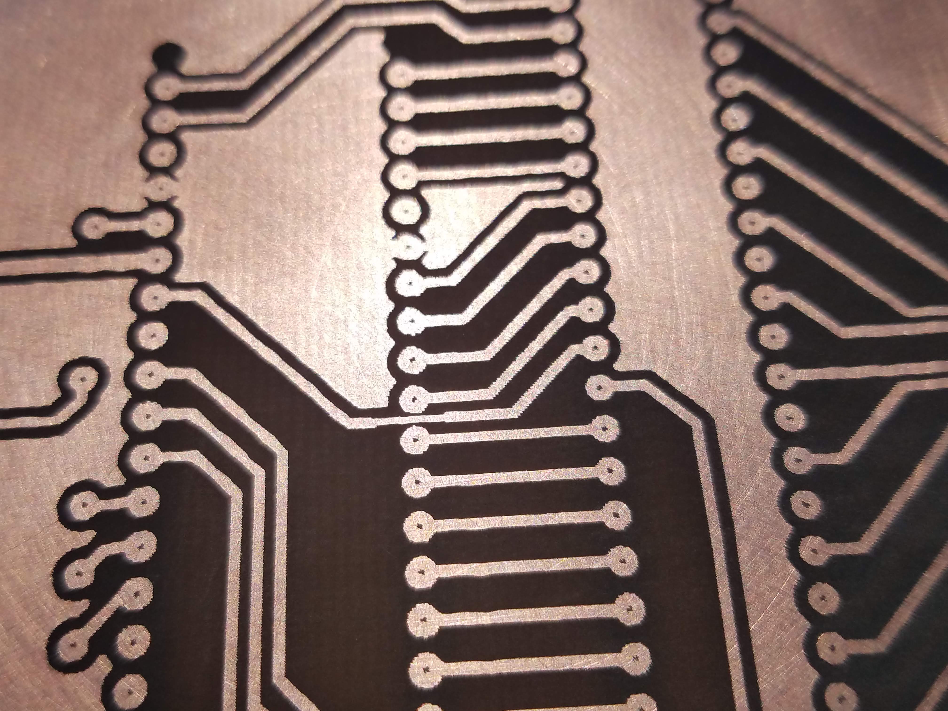
Photos/20190508_142134.jpg
