cozdas/CozScan2020/Photos/20190508_142142.jpg

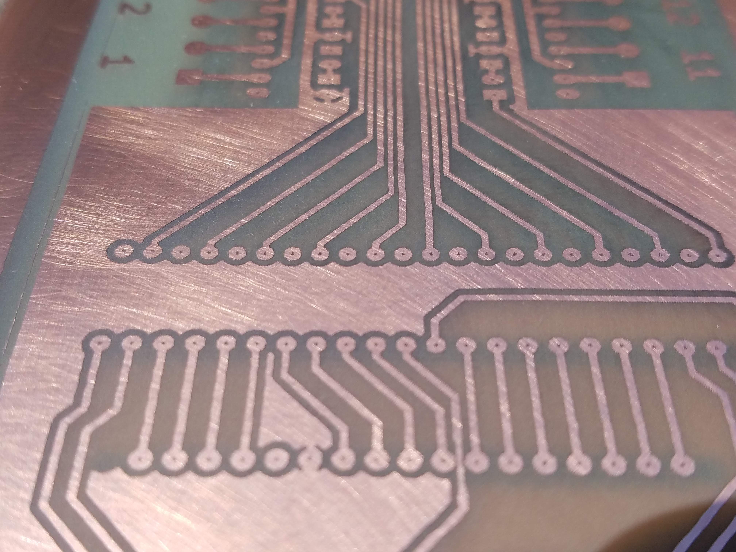
Photos/20190508_142142.jpg
