cozdas/CozScan2020/Photos/20190508_201424.jpg

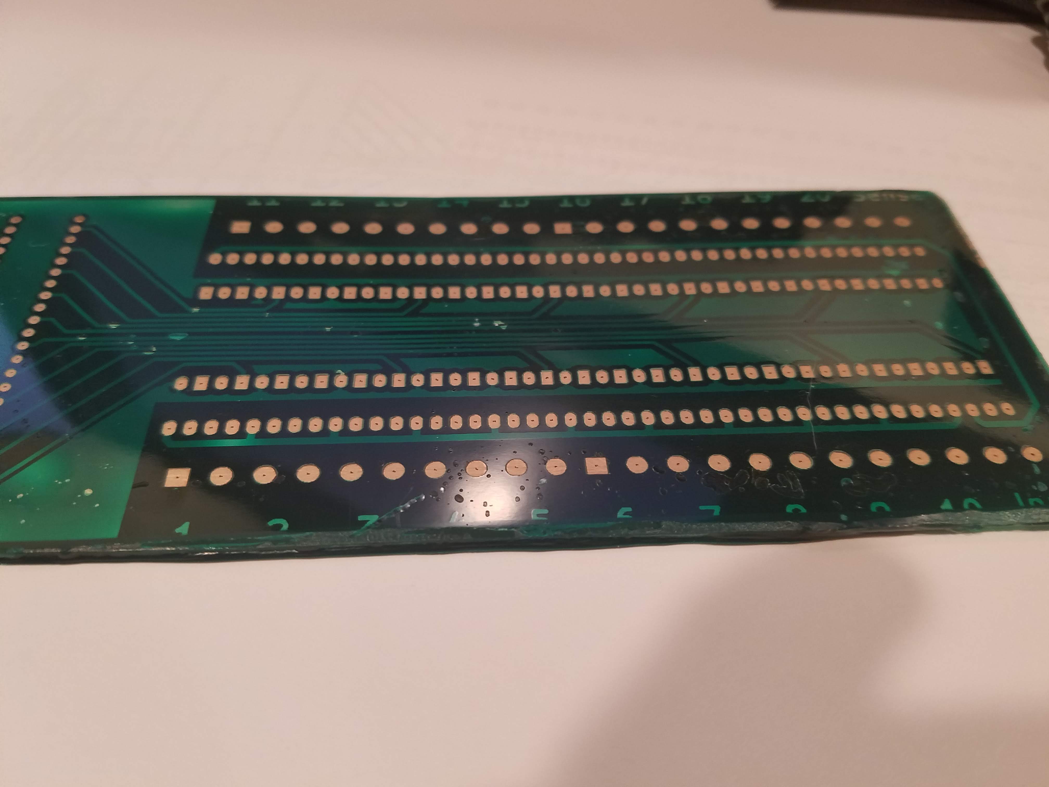
Photos/20190508_201424.jpg
