cozdas/CozScan2020/Photos/20190508_201436.jpg

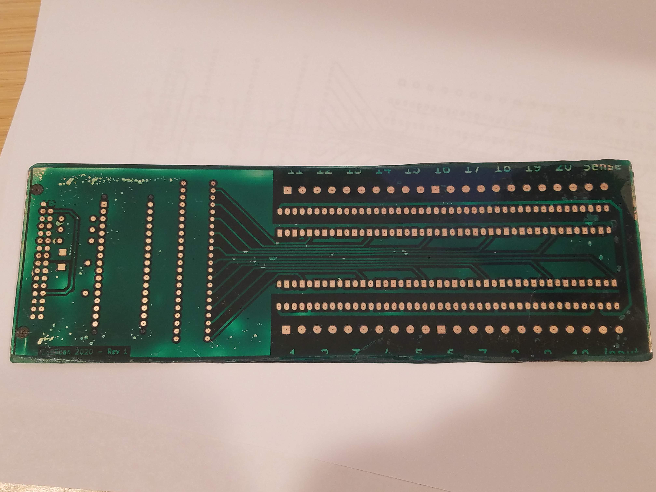
Photos/20190508_201436.jpg
