cozdas/CozScan2020/Photos/20190508_201437.jpg

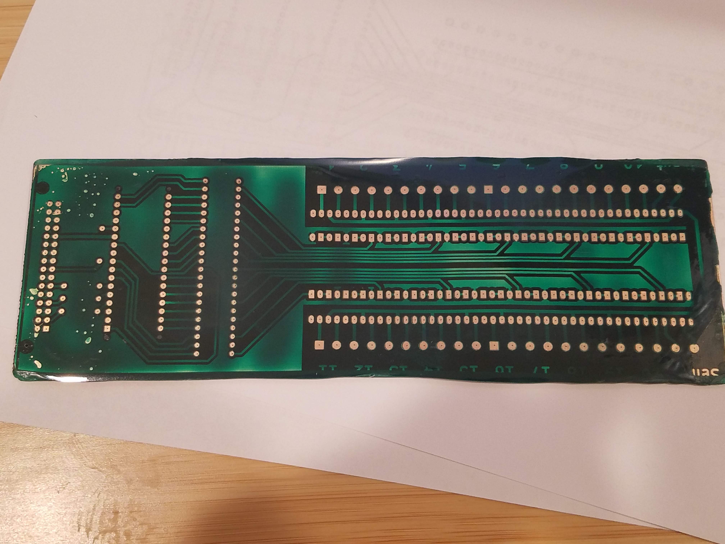
Photos/20190508_201437.jpg
