cozdas/CozScan2020/Photos/20190508_201459.jpg

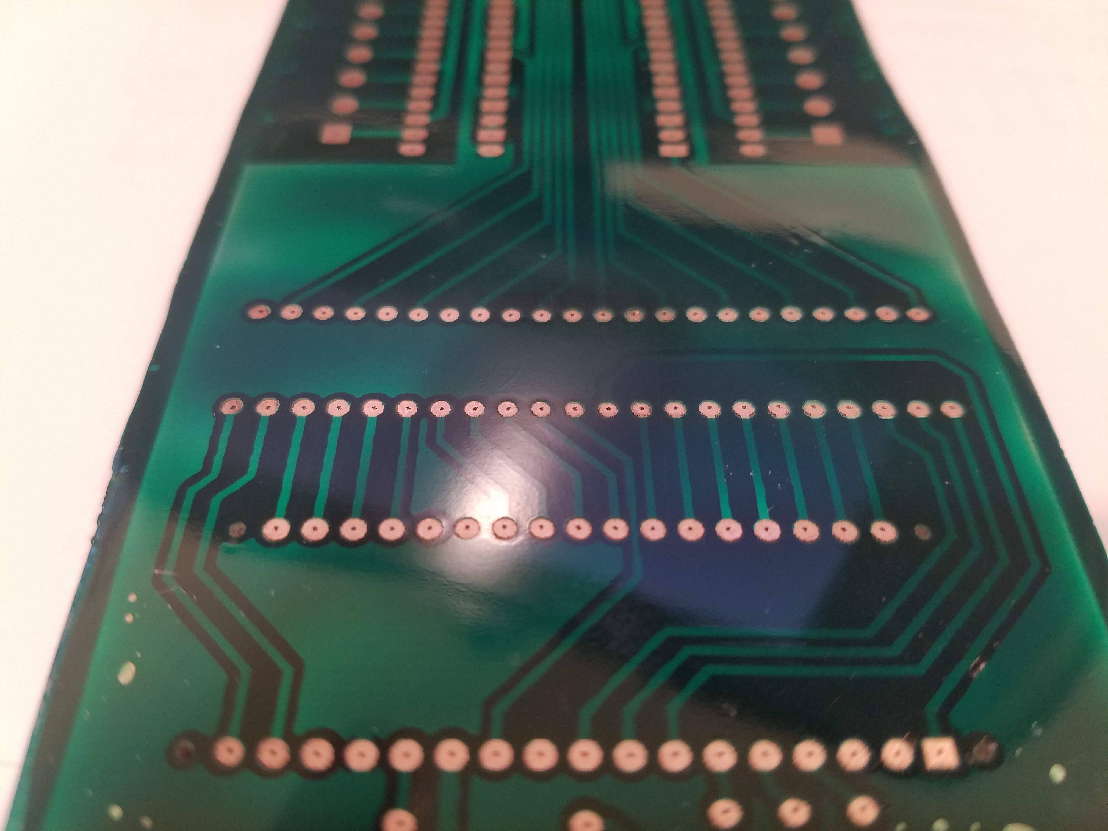
Photos/20190508_201459.jpg
