cozdas/CozScan2020/Photos/20190508_201543.jpg

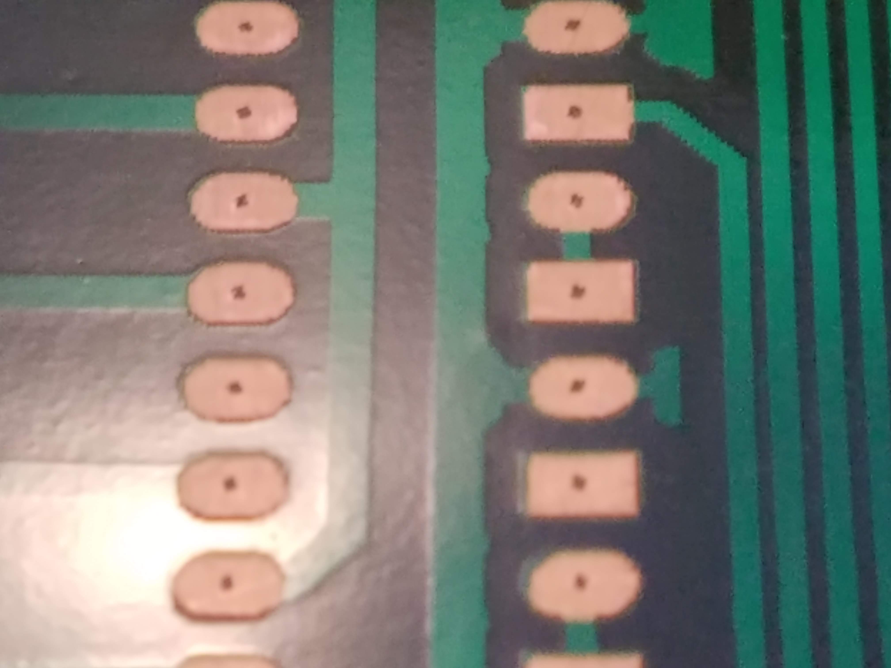
Photos/20190508_201543.jpg
