cozdas/CozScan2020/Photos/20190508_201616.jpg

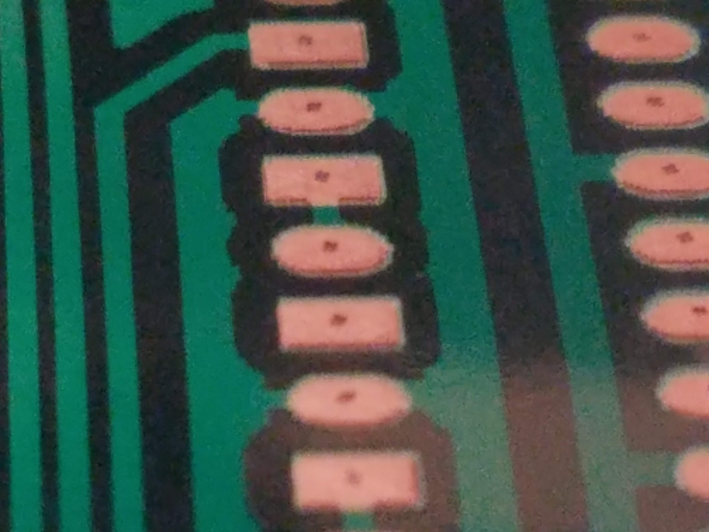
Photos/20190508_201616.jpg
