cozdas/CozScan2020/Photos/20190508_201622.jpg

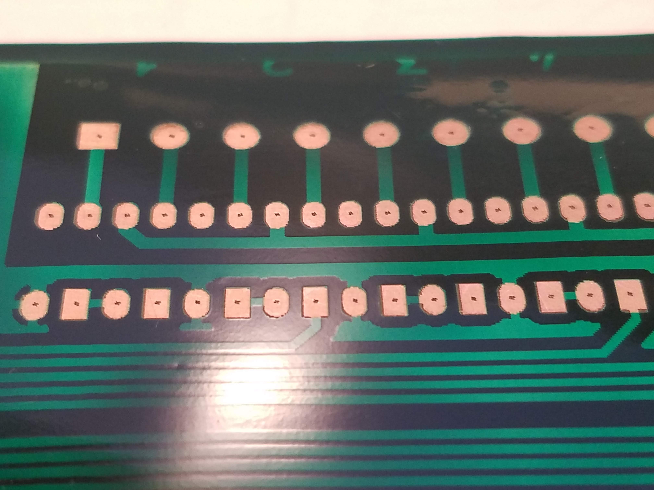
Photos/20190508_201622.jpg
