cozdas/CozScan2020/Photos/20190508_201644.jpg

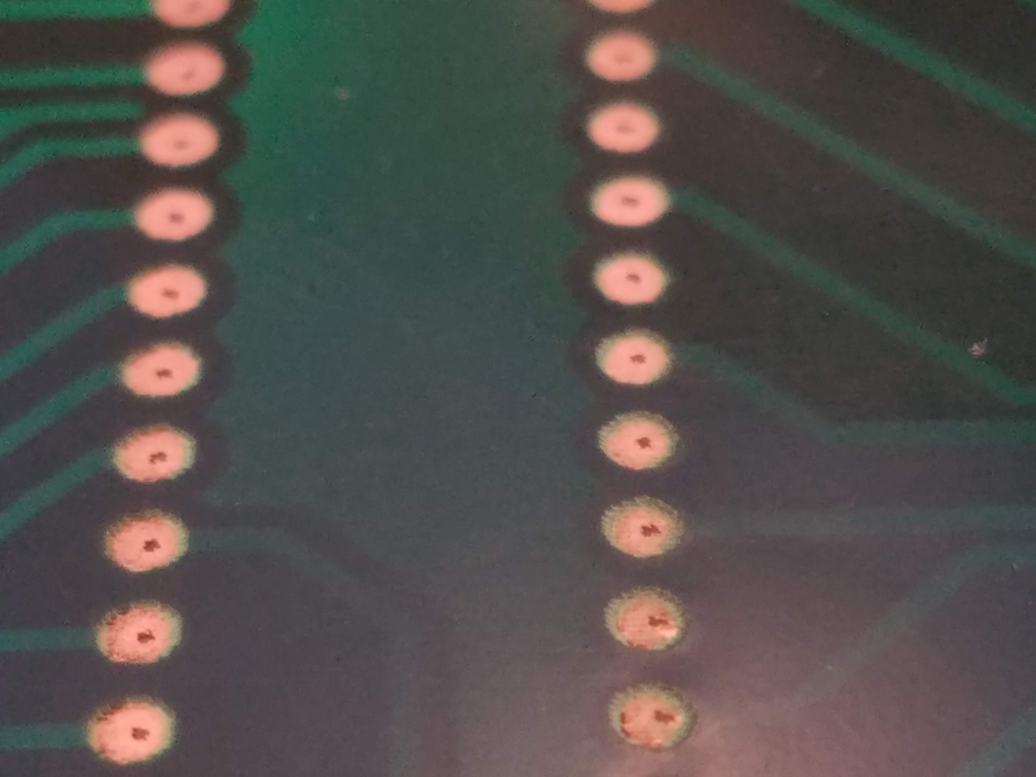
Photos/20190508_201644.jpg
