cozdas/CozScan2020/Photos/20190508_201700.jpg

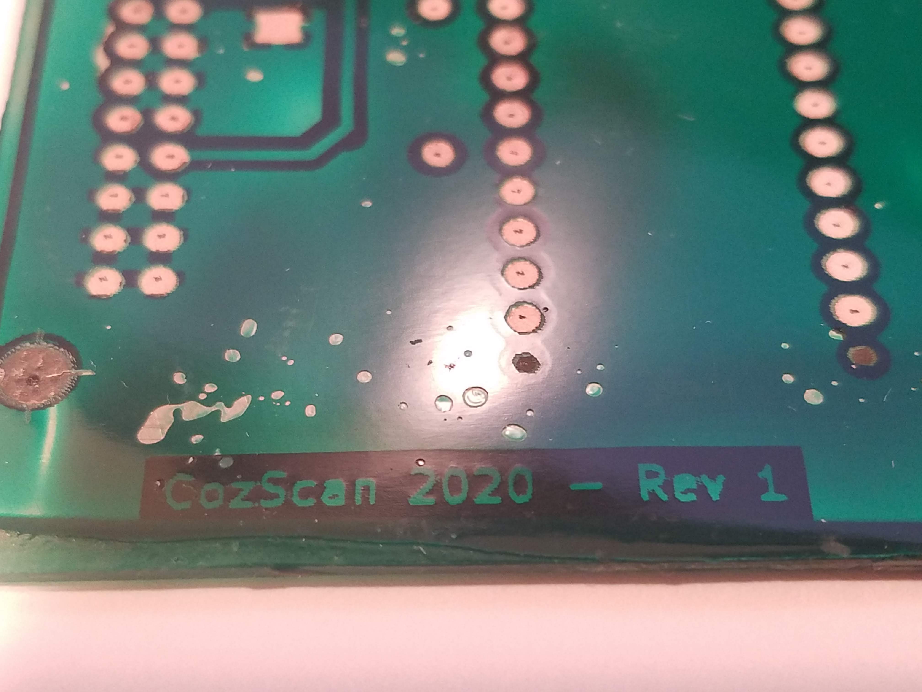
Photos/20190508_201700.jpg
