cozdas/CozScan2020/Photos/20190508_221803.jpg

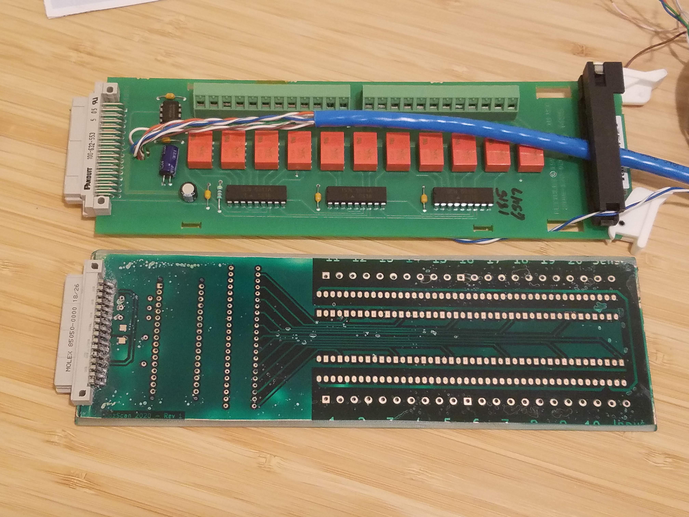
Photos/20190508_221803.jpg
