cozdas/CozScan2020/Photos/20190508_221818.jpg

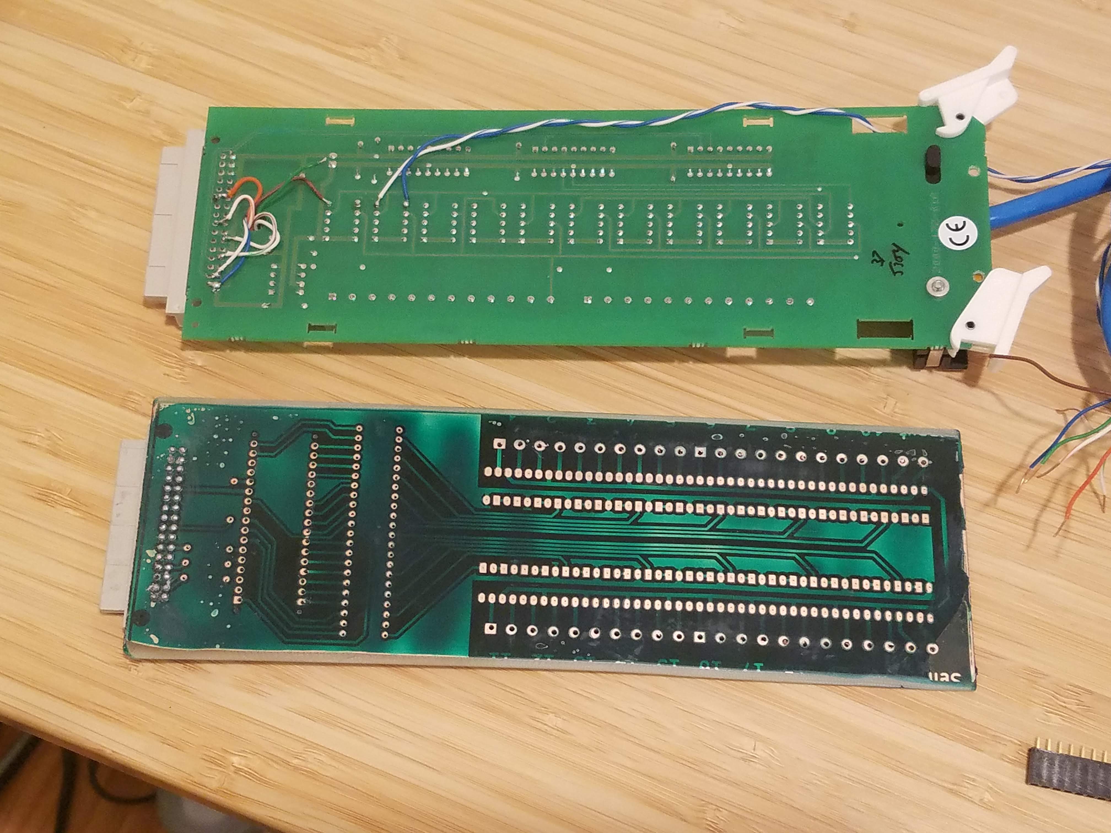
Photos/20190508_221818.jpg
