cozdas/CozScan2020/Photos/20190508_221830.jpg

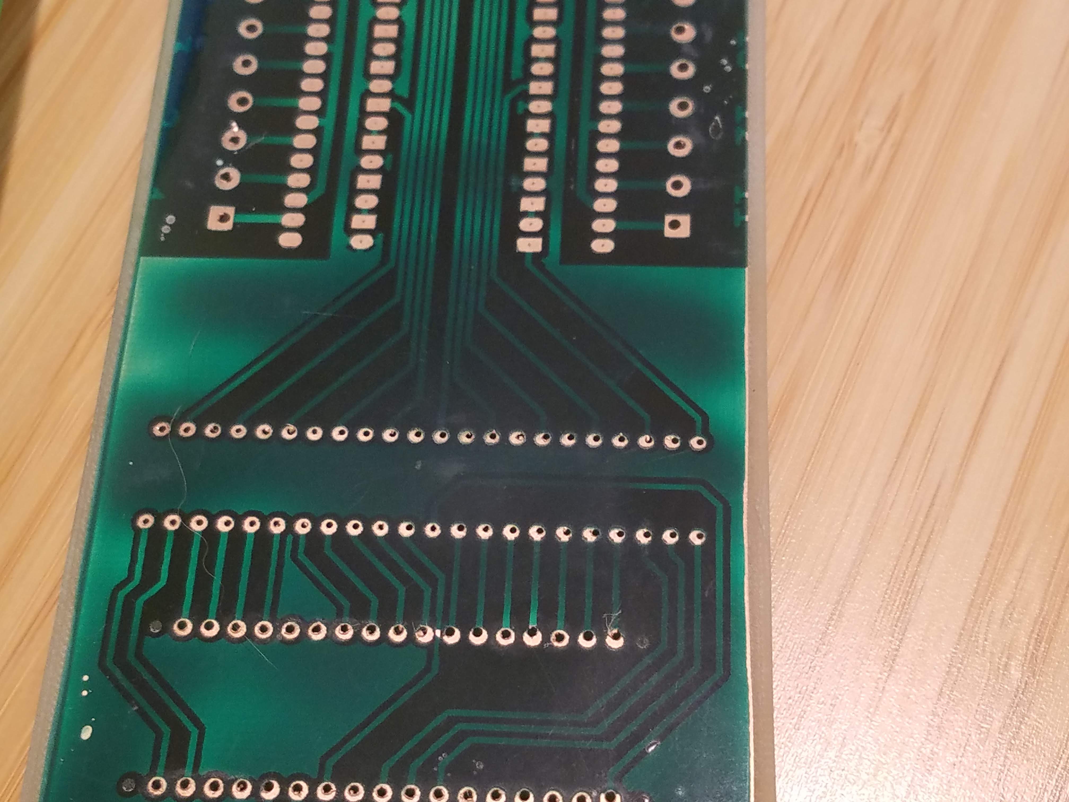
Photos/20190508_221830.jpg
