cozdas/CozScan2020/Photos/20190508_222300.jpg

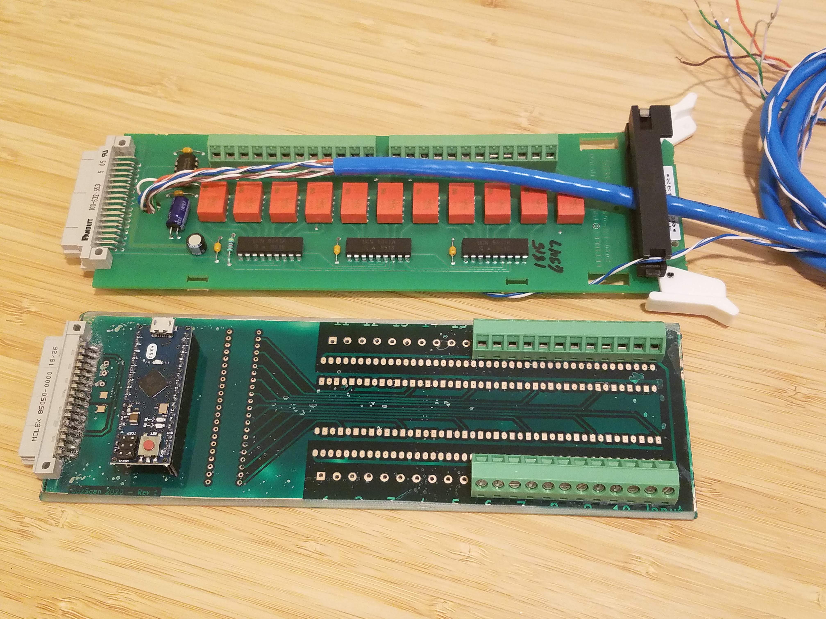
Photos/20190508_222300.jpg
