cozdas/CozScan2020/Photos/20190508_222309.jpg

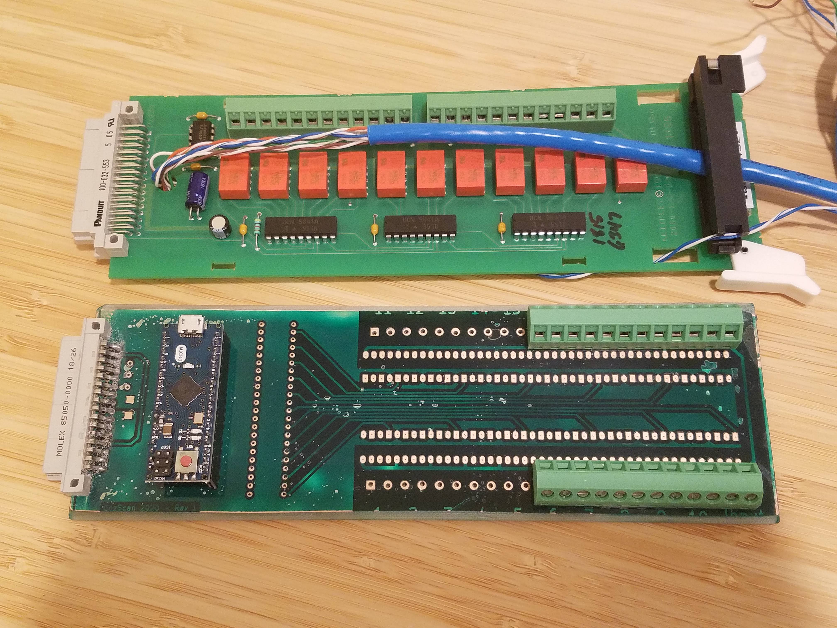
Photos/20190508_222309.jpg
