cozdas/CozScan2020/Photos/20190508_230932.jpg

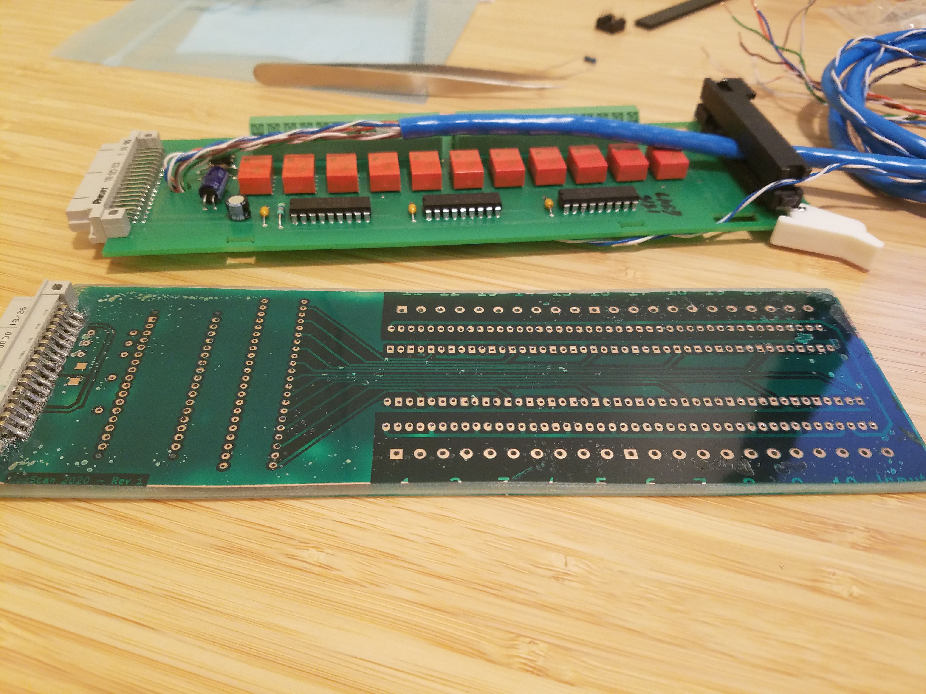
Photos/20190508_230932.jpg
