cozdas/CozScan2020/Photos/20190508_230948.jpg

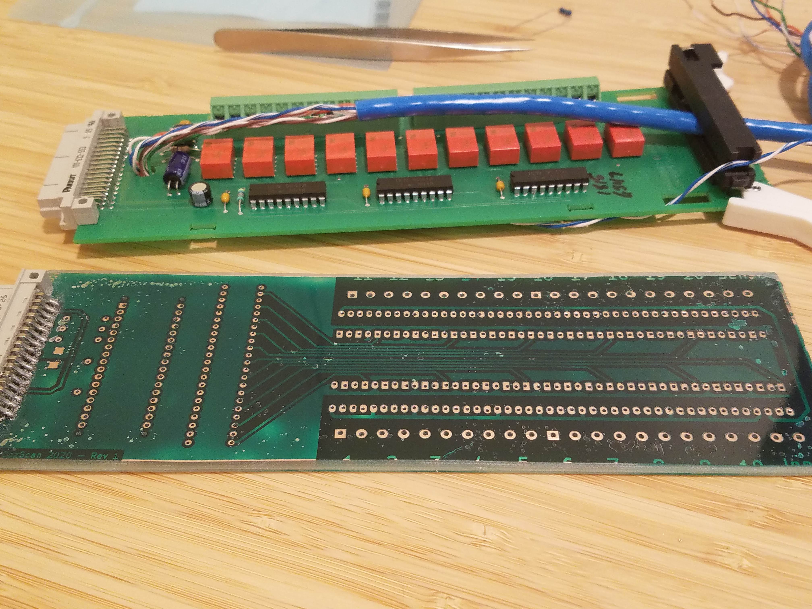
Photos/20190508_230948.jpg
