cozdas/CozScan2020/Photos/20190508_231710.jpg

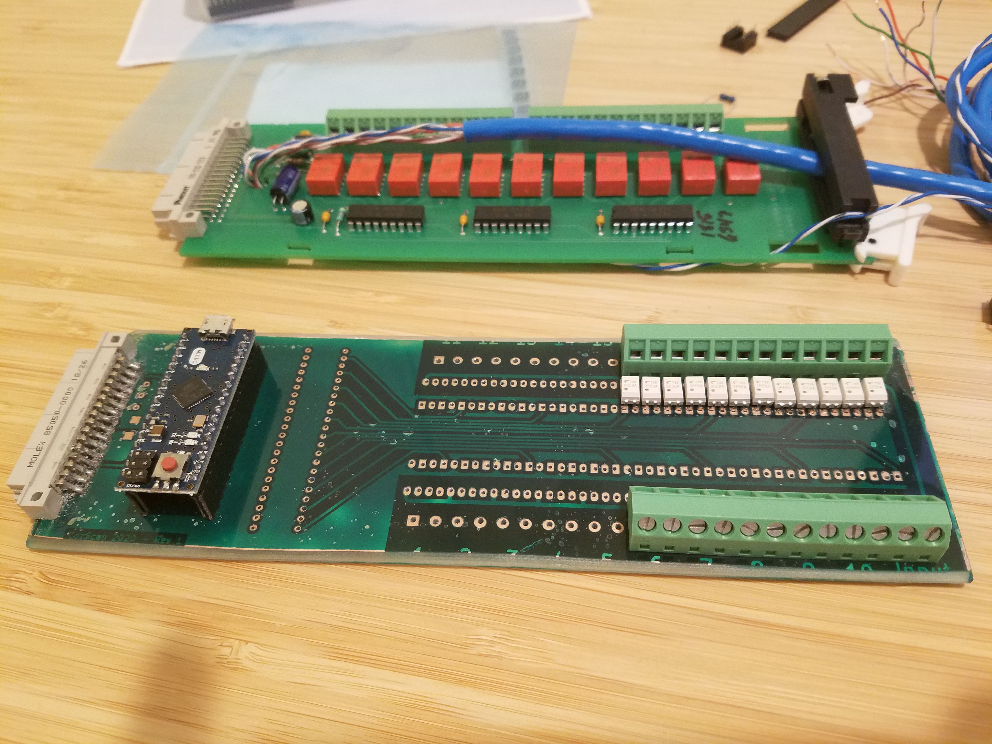
Photos/20190508_231710.jpg
