cozdas/CozScan2020/Photos/20190508_231719.jpg

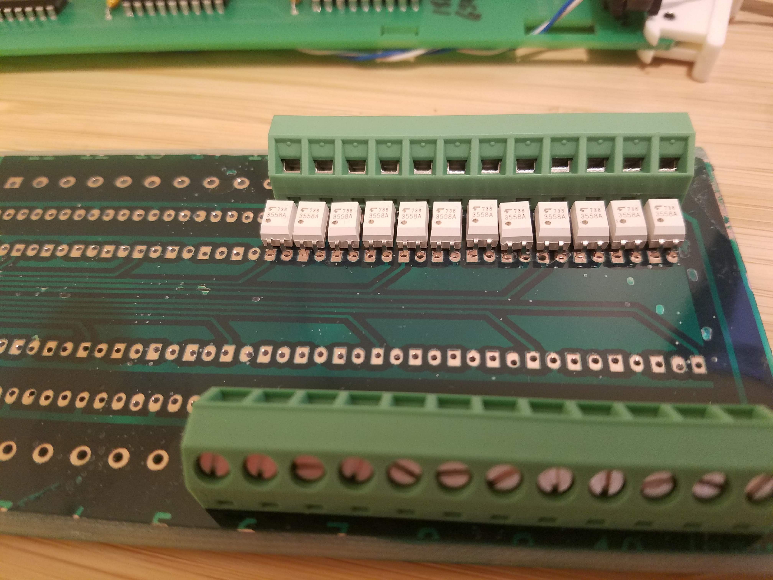
Photos/20190508_231719.jpg
