cozdas/CozScan2020/Photos/20190508_231728.jpg

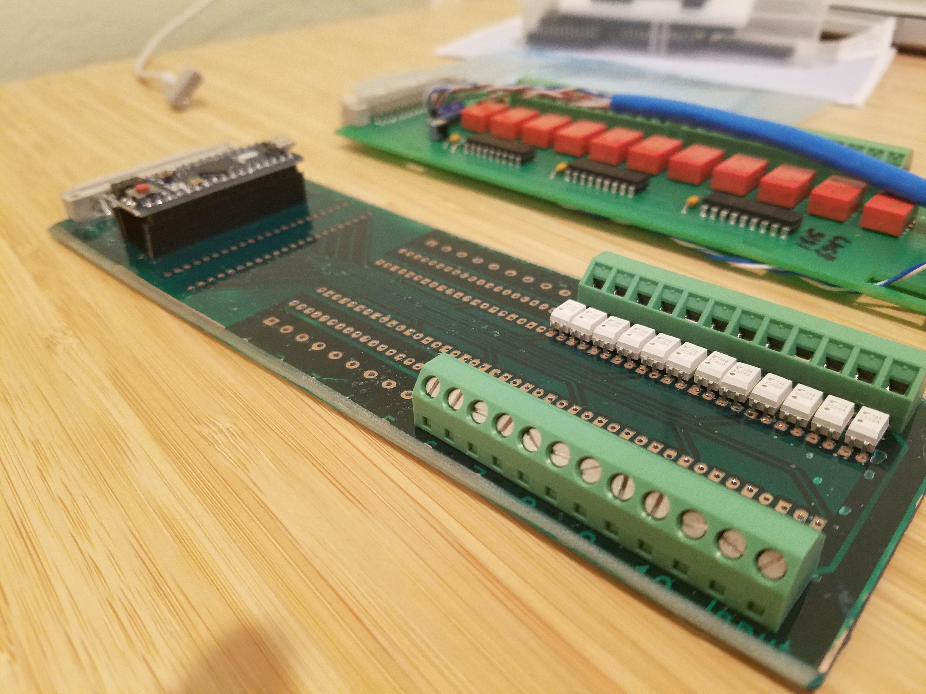
Photos/20190508_231728.jpg
