cozdas/CozScan2020/Photos/20190508_231757.jpg

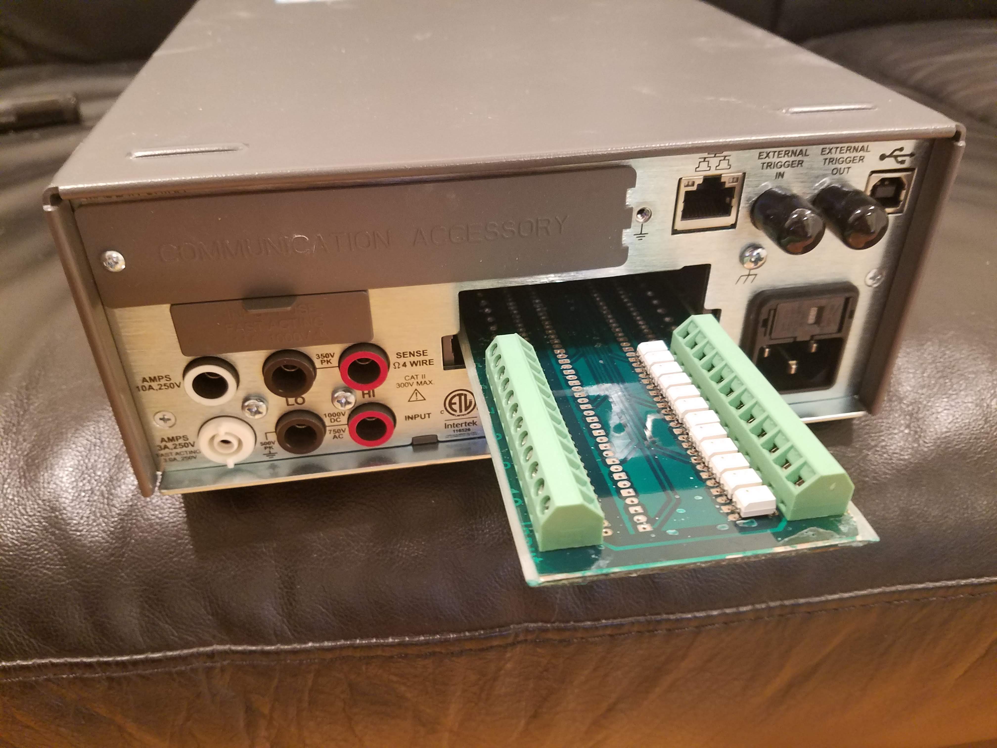
Photos/20190508_231757.jpg
