cozdas/CozScan2020/Photos/20190509_022058.jpg

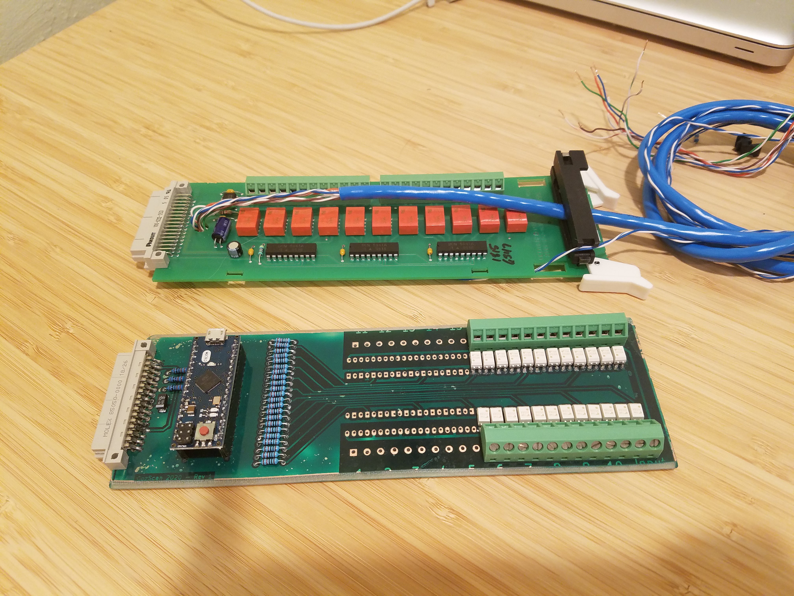
Photos/20190509_022058.jpg
