cozdas/CozScan2020/Photos/20190509_022116.jpg

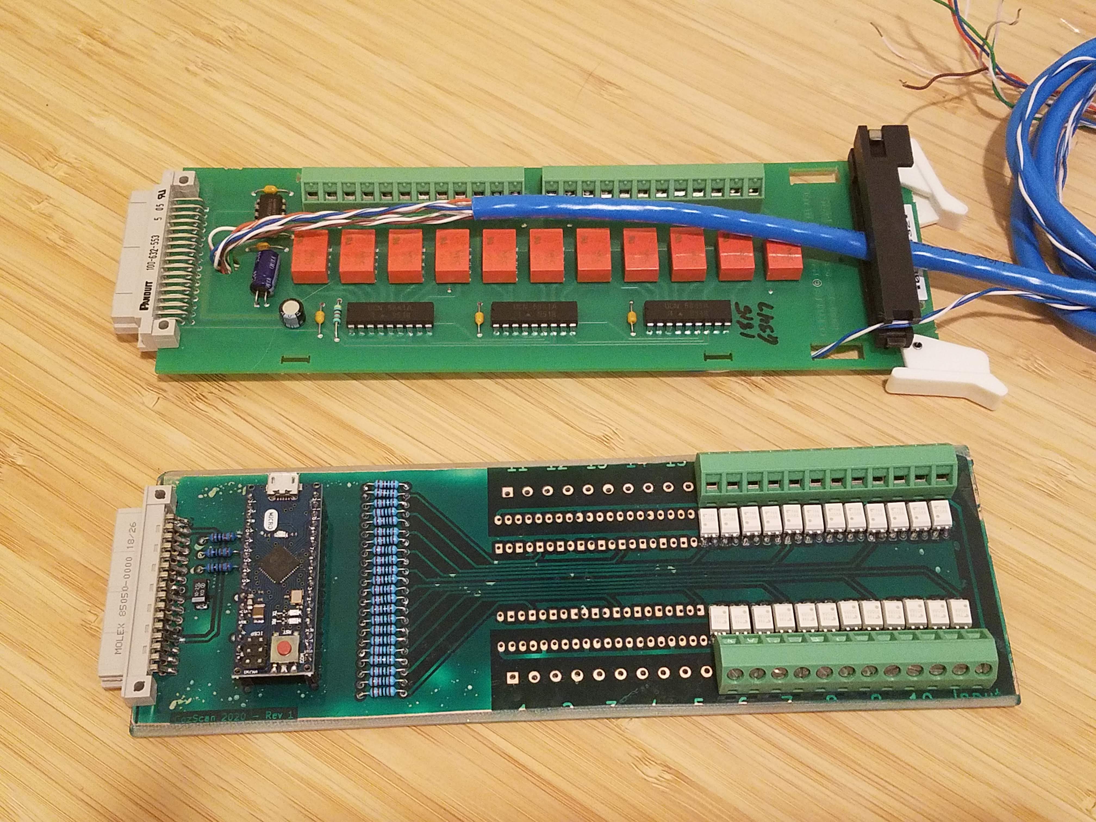
Photos/20190509_022116.jpg
