cozdas/CozScan2020/Photos/20190509_022118.jpg

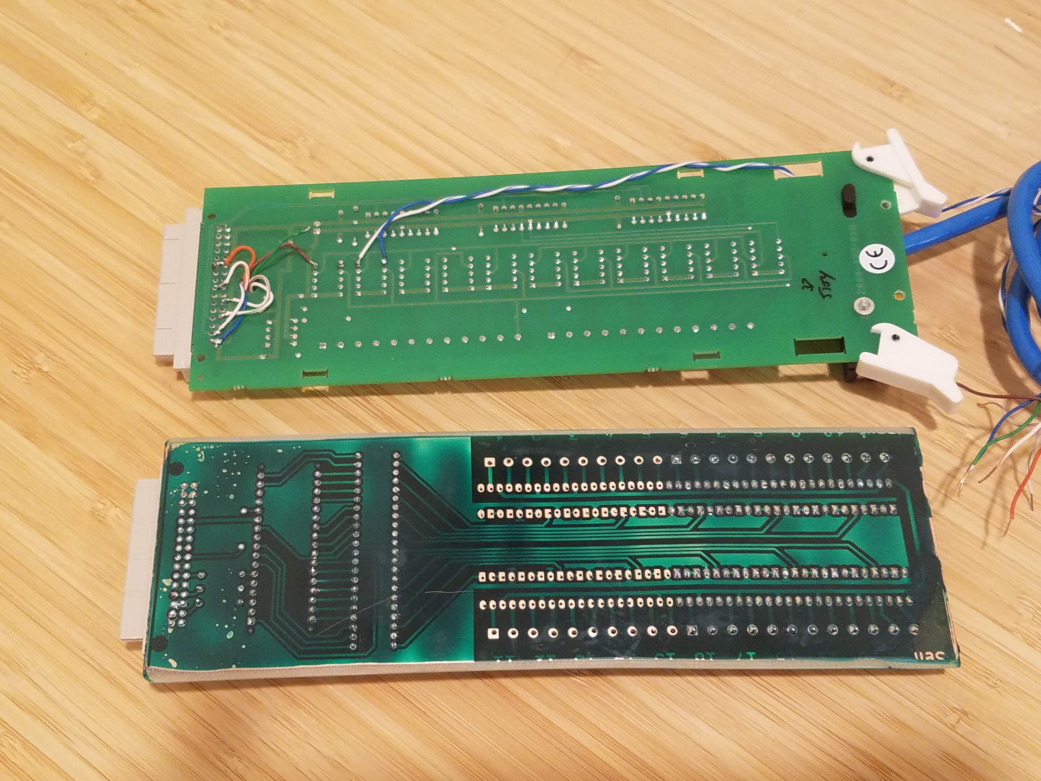
Photos/20190509_022118.jpg
