cozdas/CozScan2020/Photos/20190509_022130.jpg

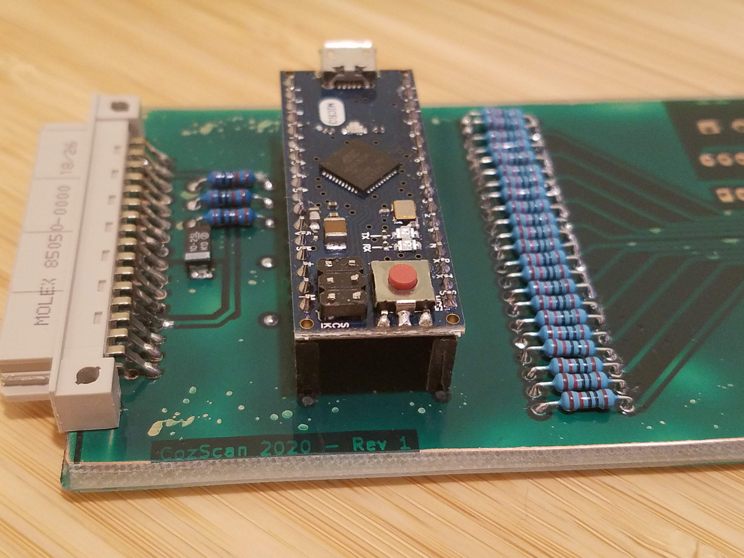
Photos/20190509_022130.jpg
