cozdas/CozScan2020/Photos/20190509_022137.jpg

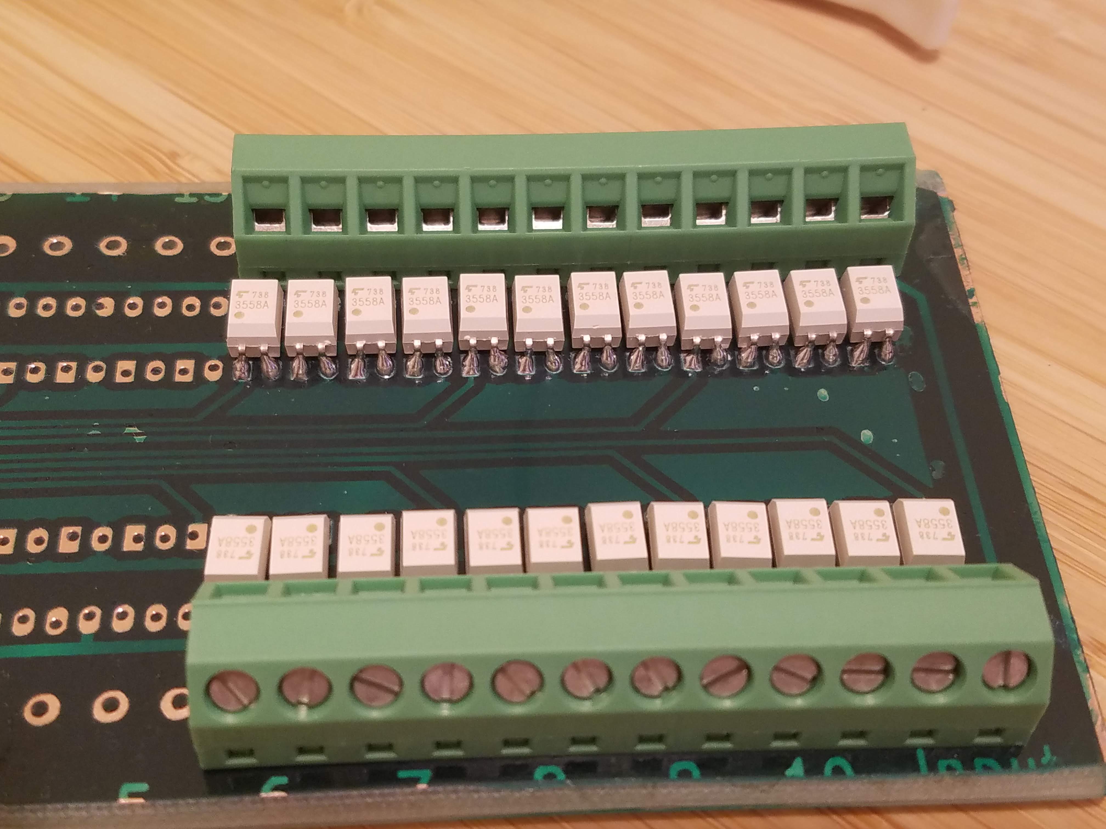
Photos/20190509_022137.jpg
