cozdas/CozScan2020/Photos/20190509_022144.jpg

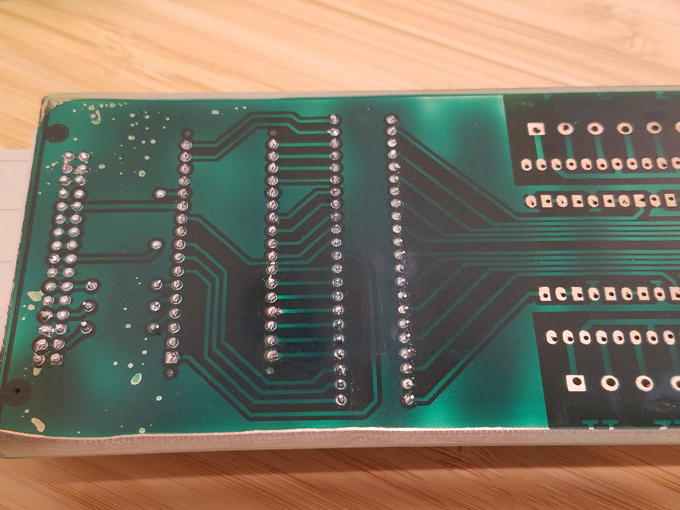
Photos/20190509_022144.jpg
