cozdas/CozScan2020/Photos/20190509_022149.jpg

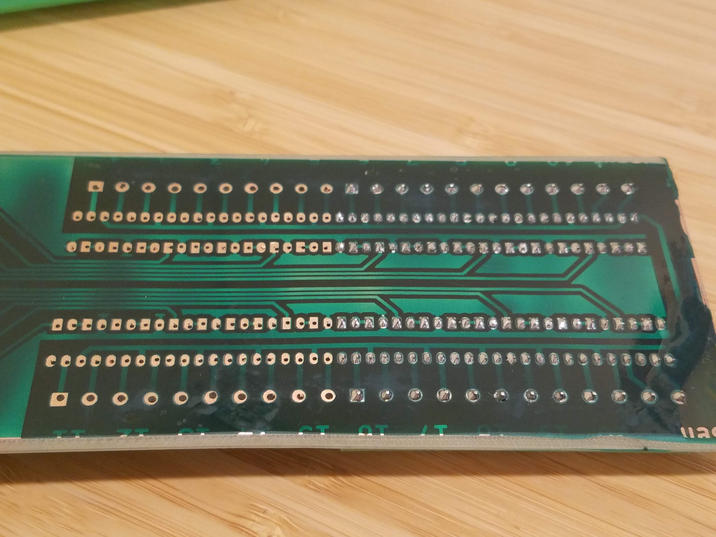
Photos/20190509_022149.jpg
