cozdas/CozScan2020/Photos/20190509_022555.jpg

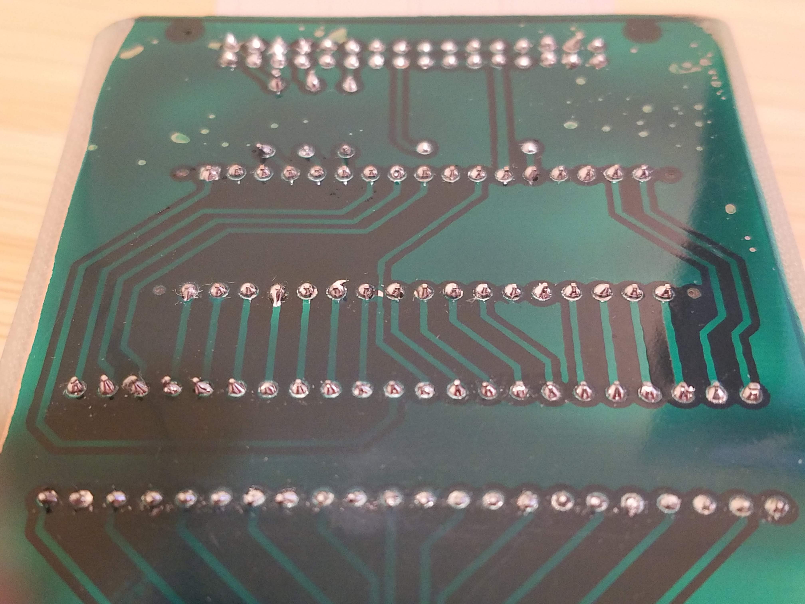
Photos/20190509_022555.jpg
