cozdas/CozScan2020/Photos/20190509_022607.jpg

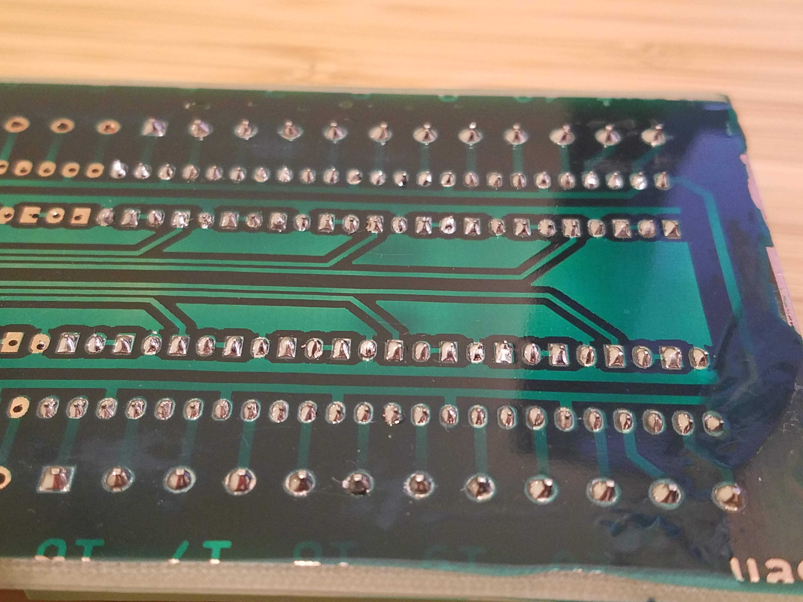
Photos/20190509_022607.jpg
