cozdas/CozScan2020/Photos/20190509_024153.jpg

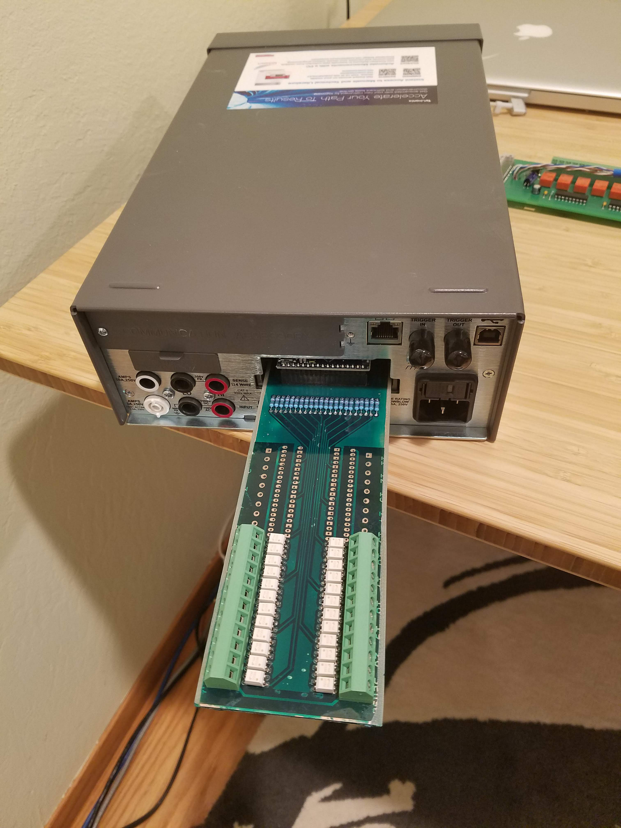
Photos/20190509_024153.jpg
