cozdas/CozScan2020/Photos/20190509_024202.jpg

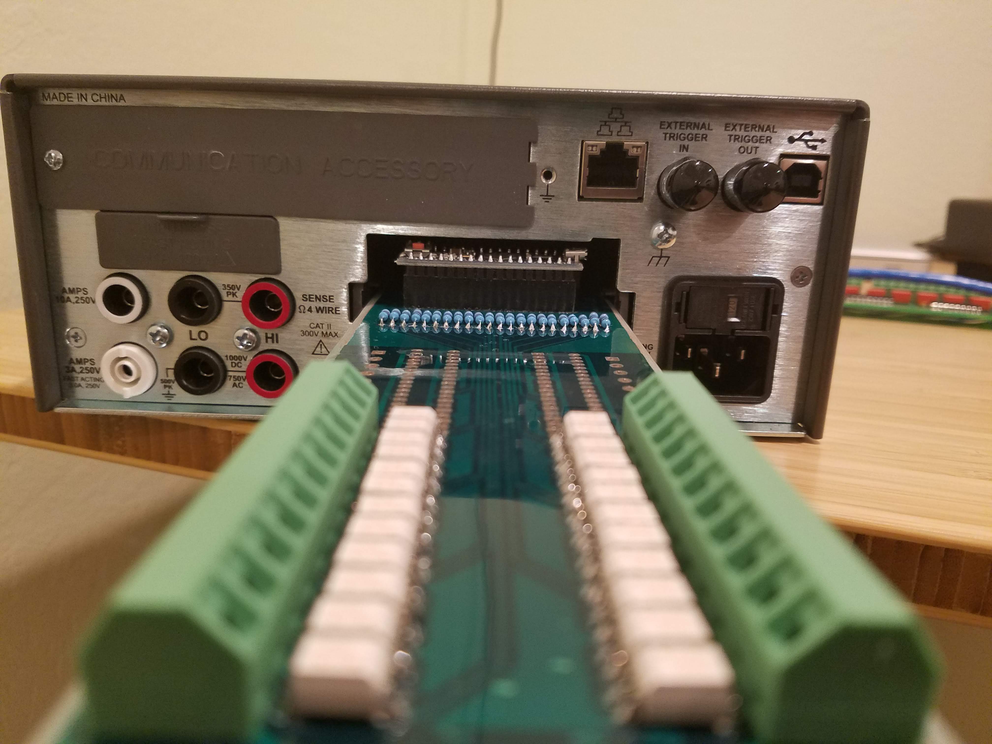
Photos/20190509_024202.jpg
