cozdas/CozScan2020/Photos/20190509_024215.jpg

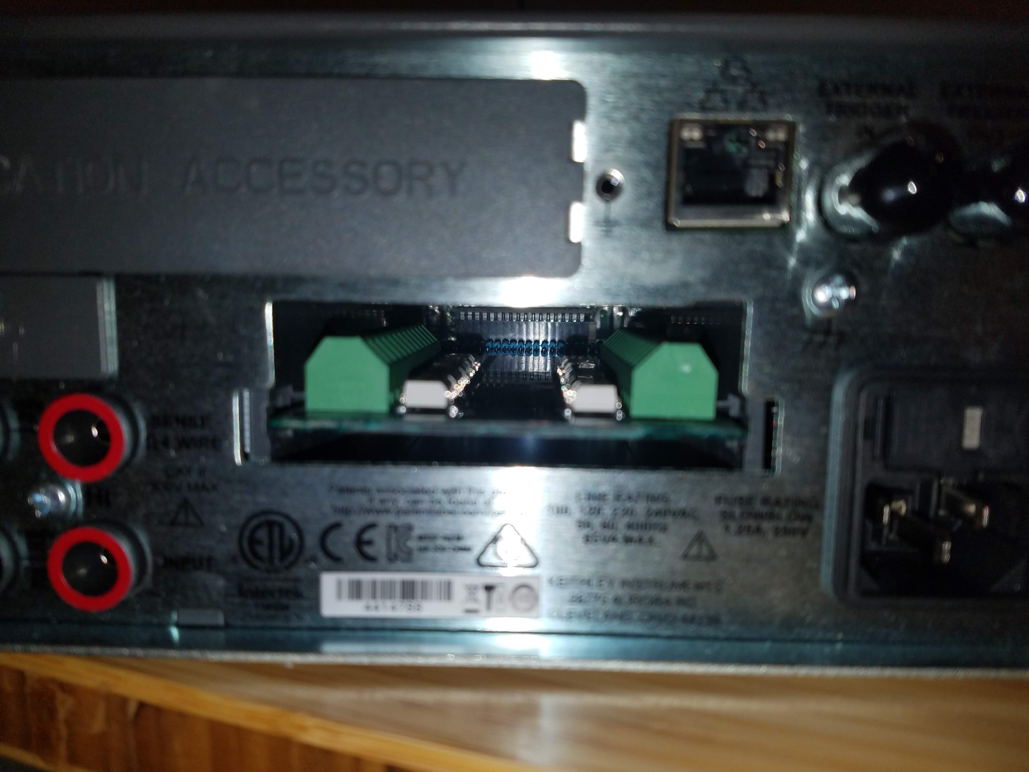
Photos/20190509_024215.jpg
