cozdas/CozScan2020/Photos/20190509_024318.jpg

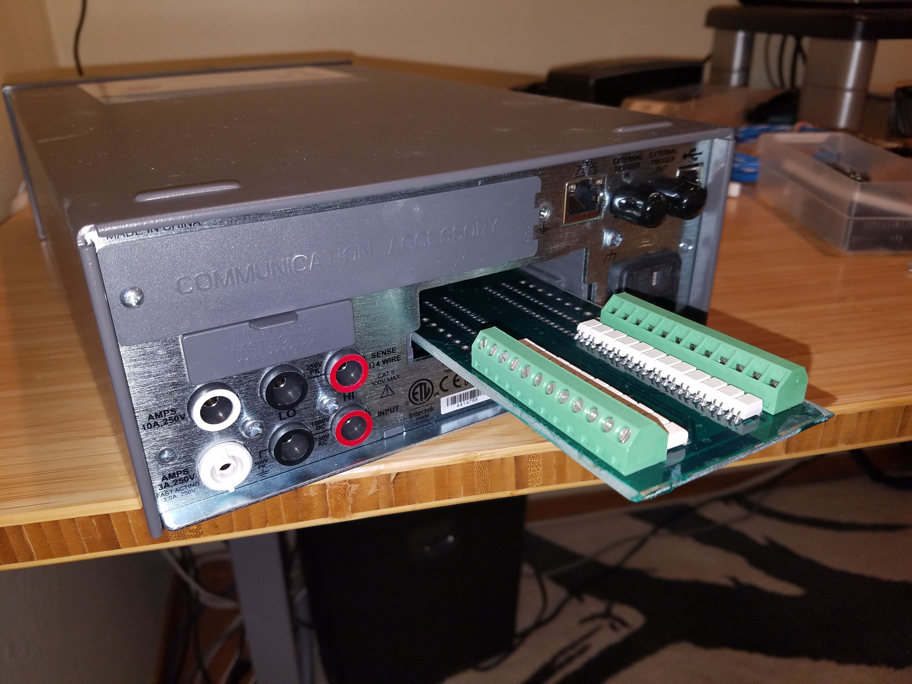
Photos/20190509_024318.jpg
