cozdas/CozScan2020/Photos/20190509_024325.jpg

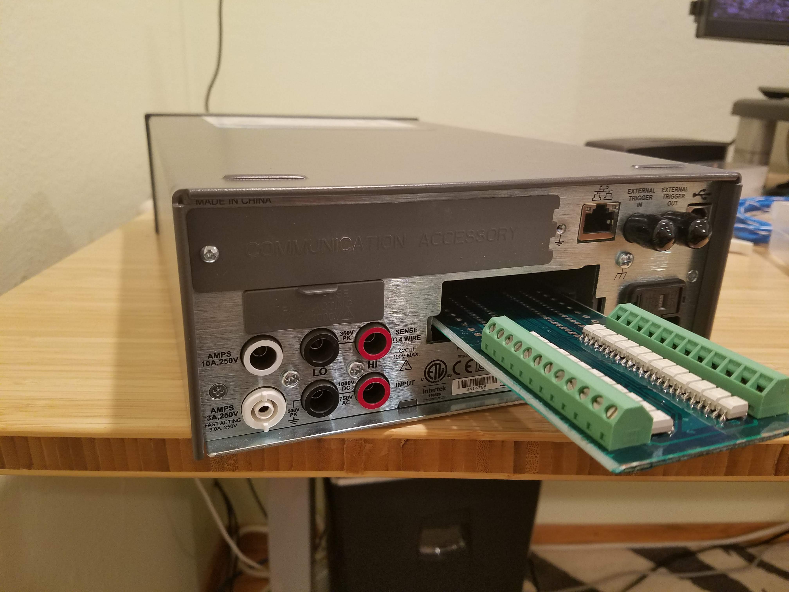
Photos/20190509_024325.jpg
