cozdas/CozScan2020/Photos/20190509_024328.jpg

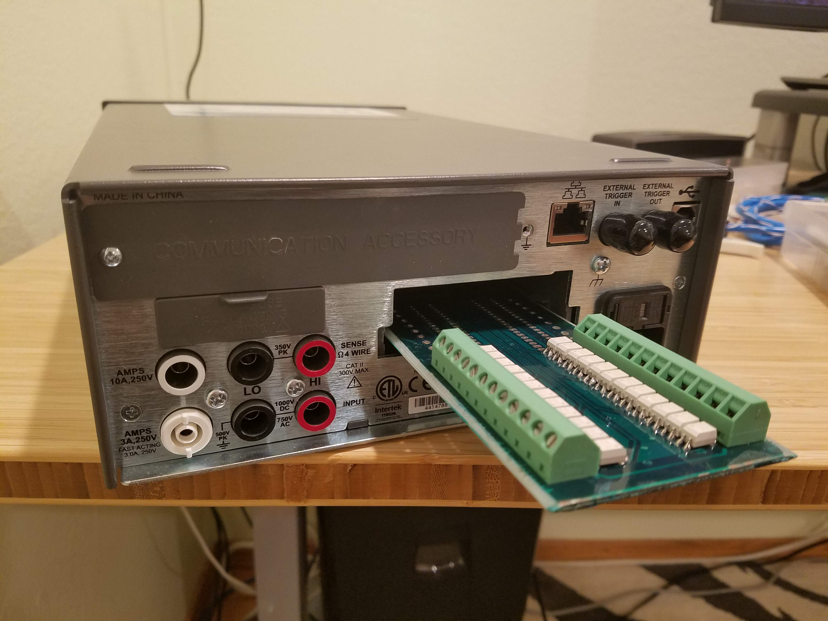
Photos/20190509_024328.jpg
