cozdas/CozScan2020/Photos/IMG_20191224_010619.jpg

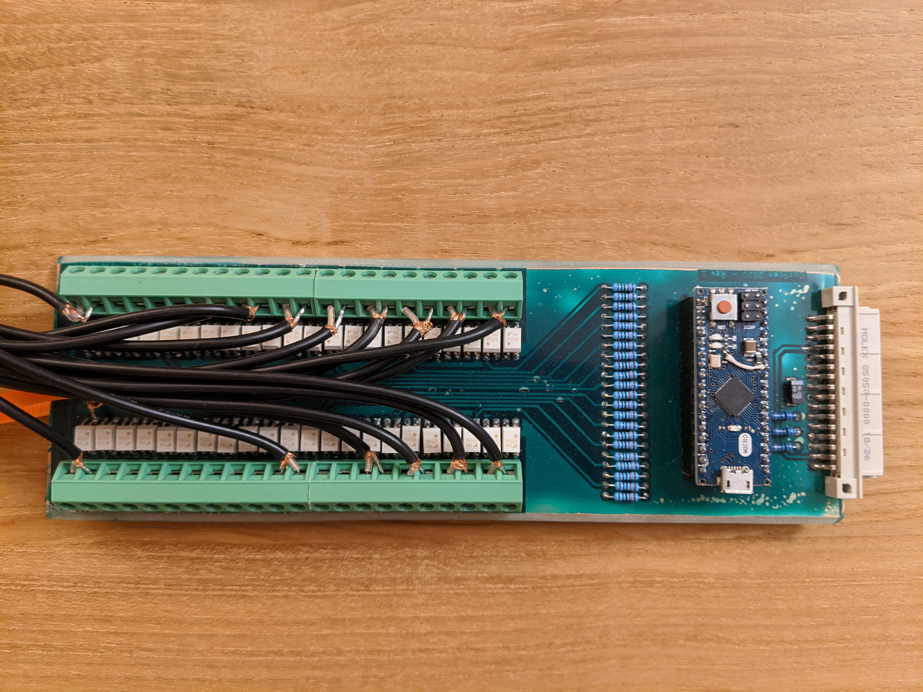
Photos/IMG_20191224_010619.jpg
