cozdas/CozScan2020/Photos/Scan2020_timing_02.jpg

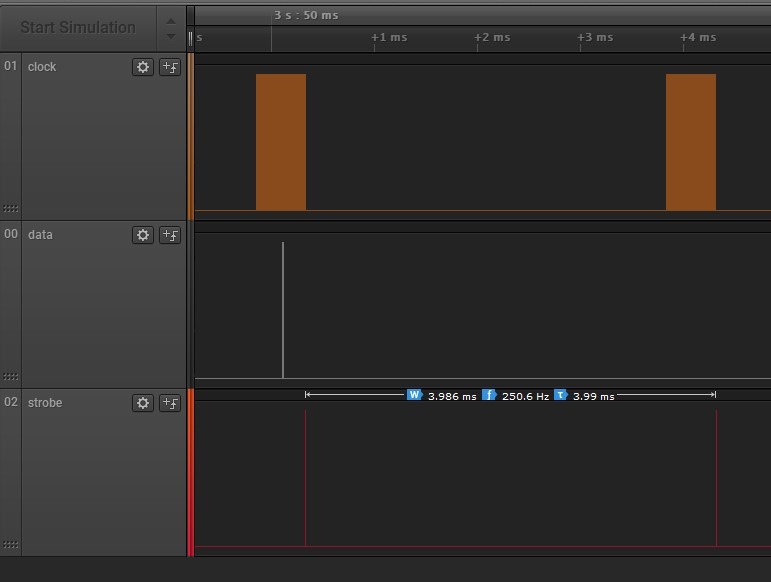
Photos/Scan2020_timing_02.jpg
