cozdas/CozScan2020/Photos/Scan2020_timing_chan-to-chan.jpg

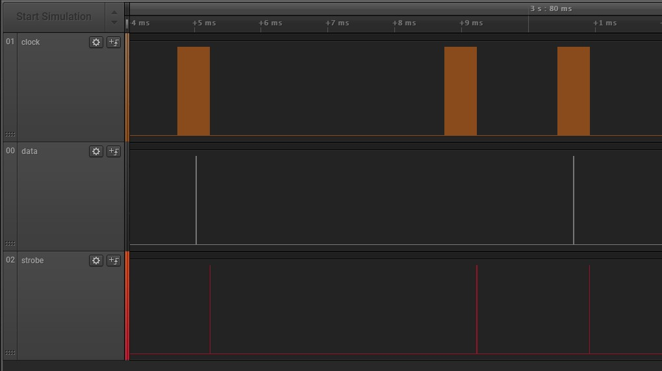
Photos/Scan2020_timing_chan-to-chan.jpg
